gulyasyalex/Proiect-NXP-CUP-2025-/Teensy-Code/Images/20240411_223237.jpg

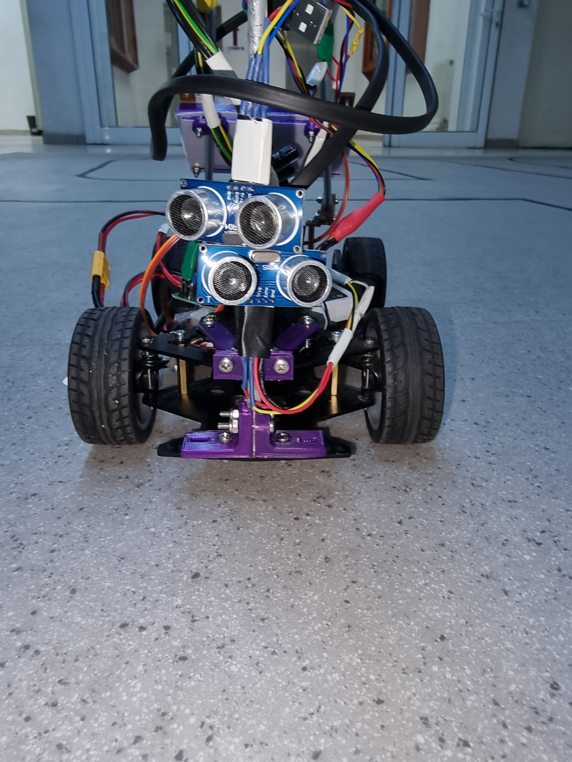
Teensy-Code/Images/20240411_223237.jpg
