gulyasyalex/Proiect-NXP-CUP-2025-/Teensy-Code/Images/20240411_223405.jpg

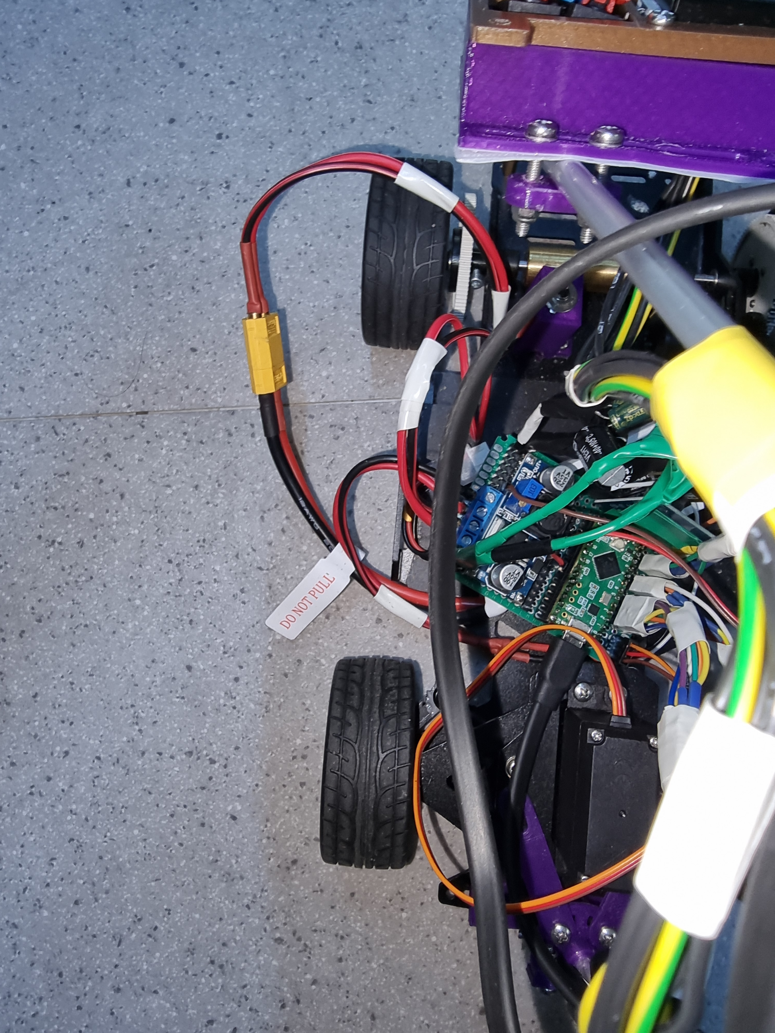
Teensy-Code/Images/20240411_223405.jpg
