gulyasyalex/Proiect-NXP-CUP-2025-/Teensy-Code/Images/20240411_223413.jpg

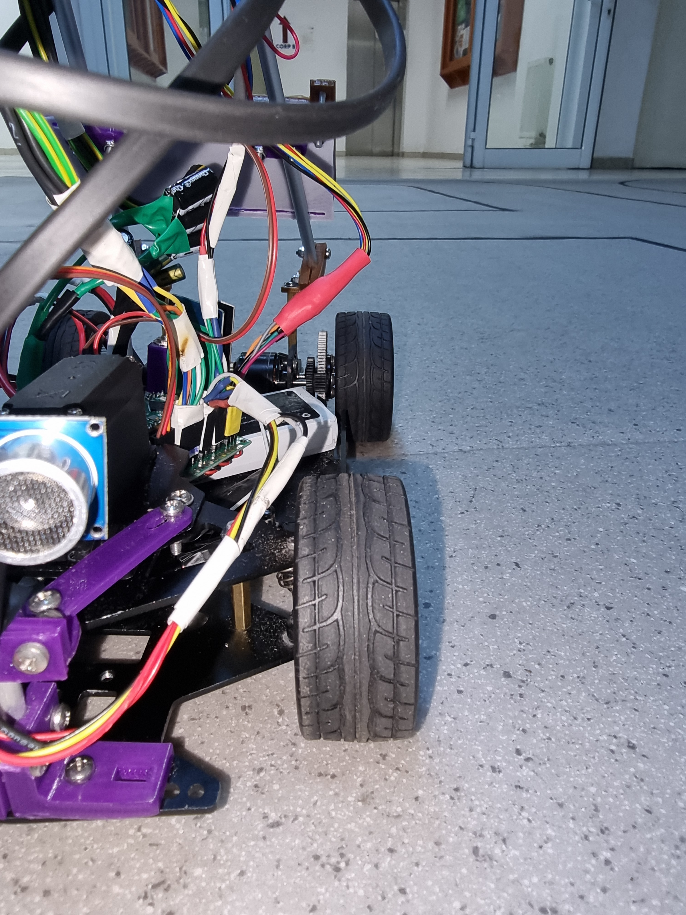
Teensy-Code/Images/20240411_223413.jpg
