gulyasyalex/Proiect-NXP-CUP-2025-/Teensy-Code/Images/20240411_223524.jpg

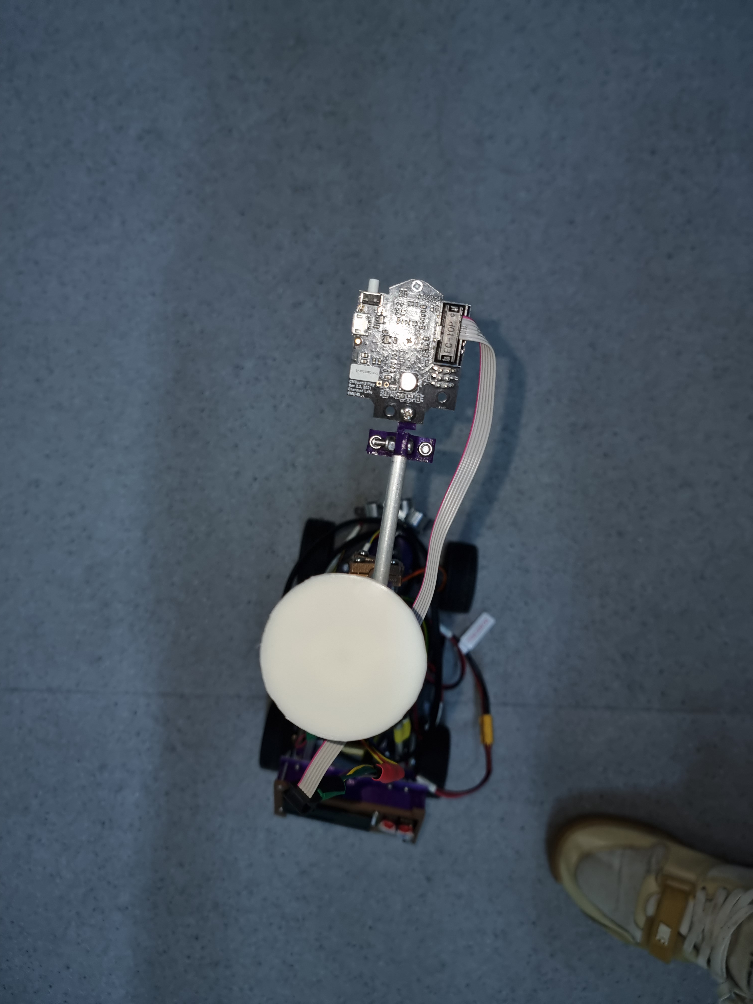
Teensy-Code/Images/20240411_223524.jpg
