gulyasyalex/Proiect-NXP-CUP-2025-/Teensy-Code/Images/car.jpg

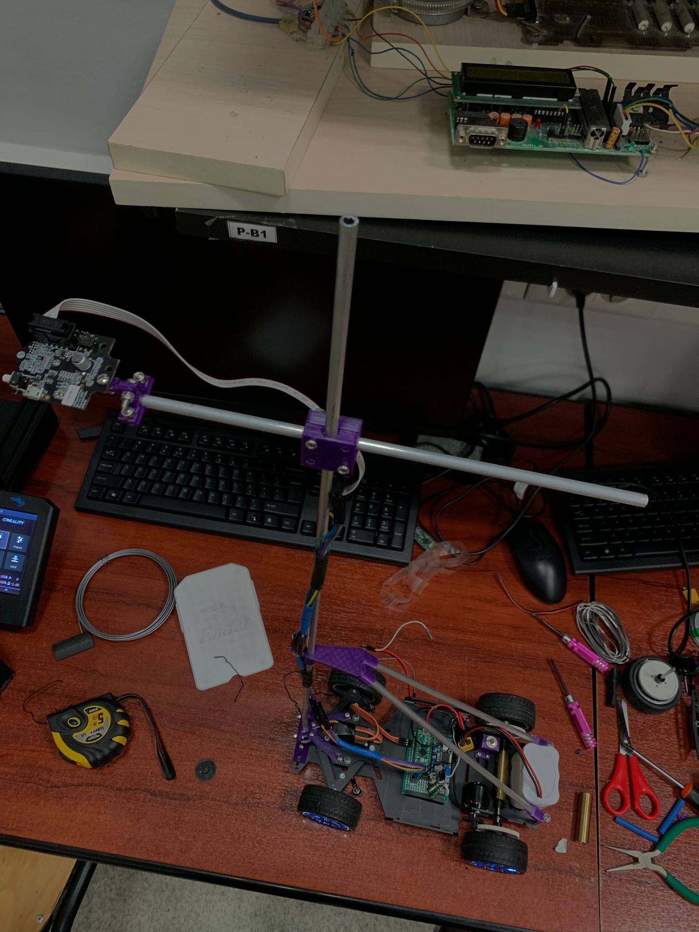
Teensy-Code/Images/car.jpg
