gulyasyalex/Proiect-NXP-CUP-2025-/Teensy-Code/Images/carMenu1.jpg

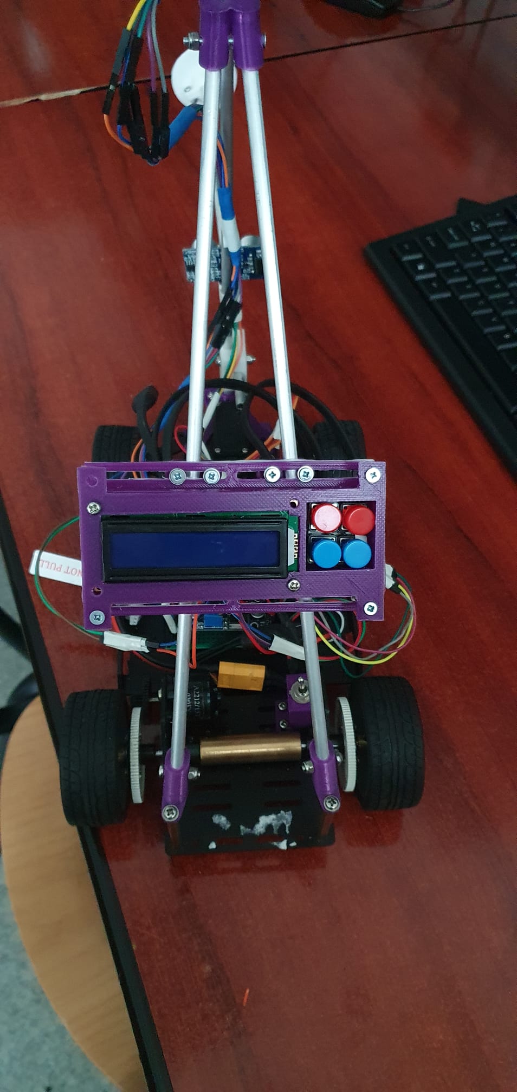
Teensy-Code/Images/carMenu1.jpg
