gulyasyalex/Proiect-NXP-CUP-2025-/Teensy-Code/Images/CarMenu.jpg

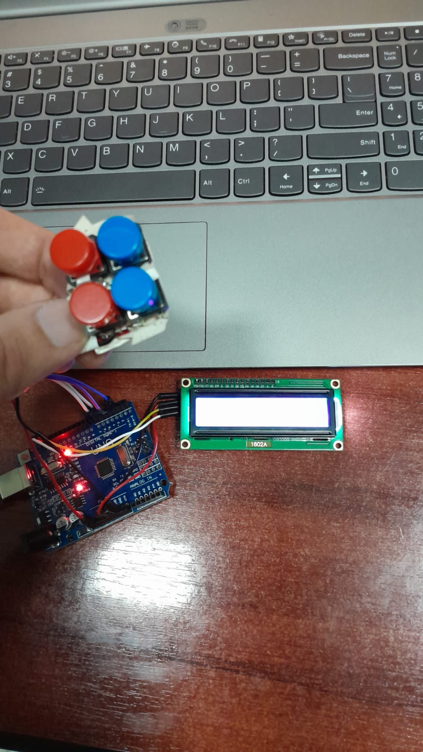
Teensy-Code/Images/CarMenu.jpg
