gulyasyalex/Proiect-NXP-CUP-2025-/Teensy-Code/Images/CarPcb.jpg

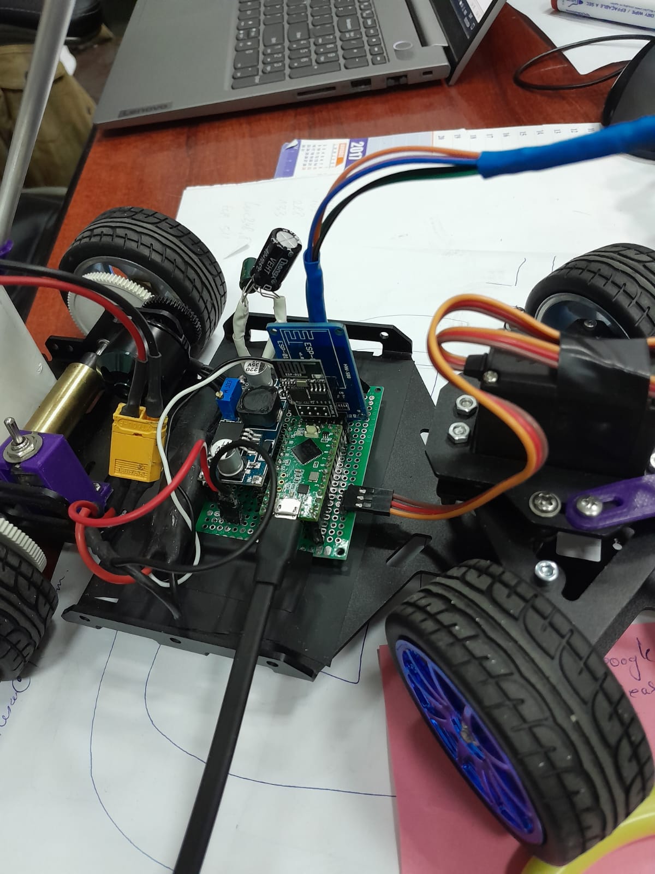
Teensy-Code/Images/CarPcb.jpg
