gulyasyalex/Proiect-NXP-CUP-2025-/Teensy-Code/Images/carVersion3.jpg

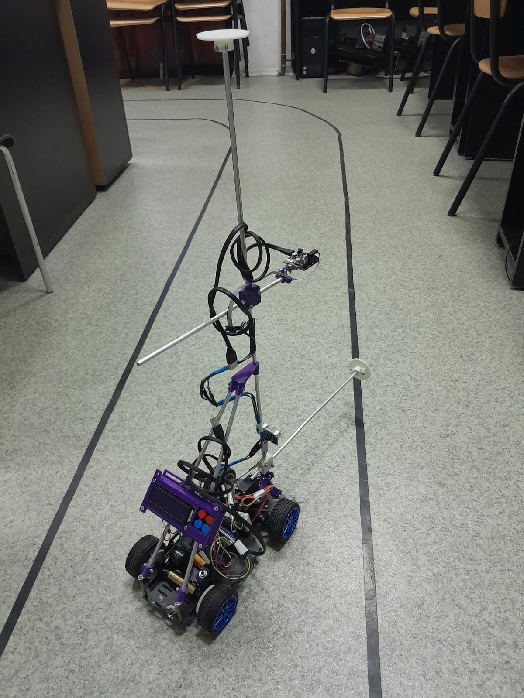
Teensy-Code/Images/carVersion3.jpg
