gulyasyalex/Proiect-NXP-CUP-2025-/Teensy-Code/Images/lcd_menu_support.png

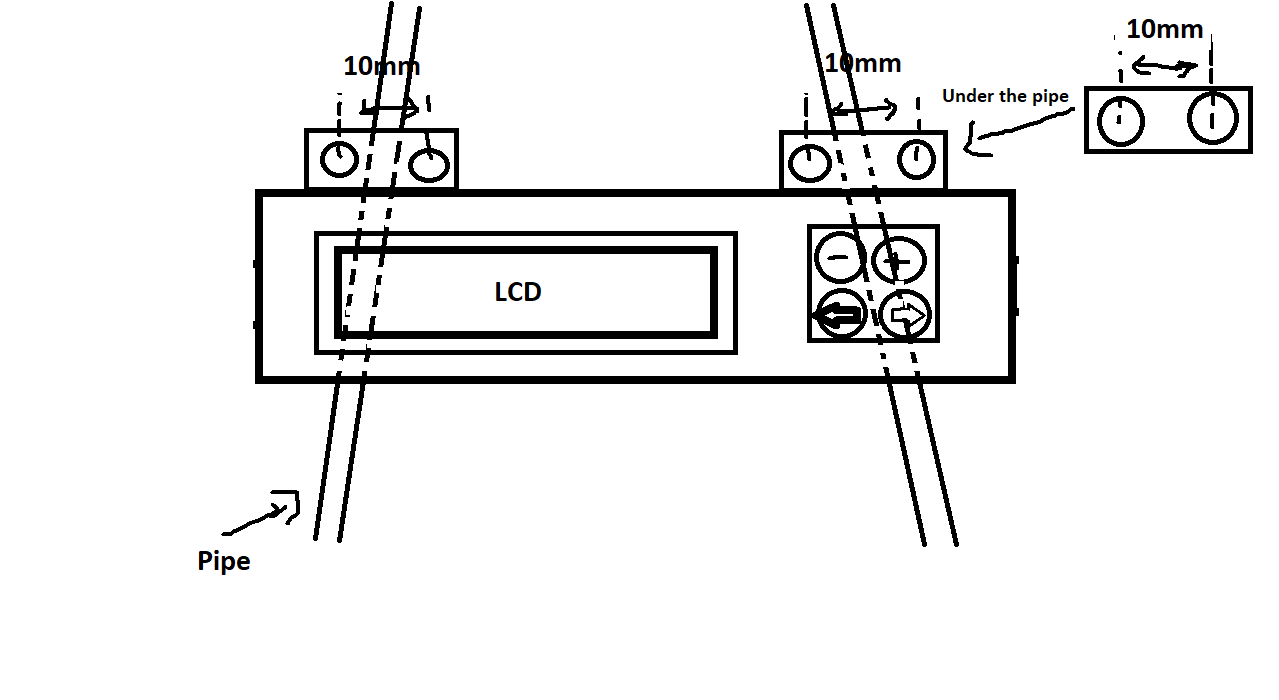
Teensy-Code/Images/lcd_menu_support.png
