gulyasyalex/Proiect-NXP-CUP-2025-/Teensy-Code/PCB-Kicad/Modul_Lcd_Butoane/lcd3dModel.jpeg

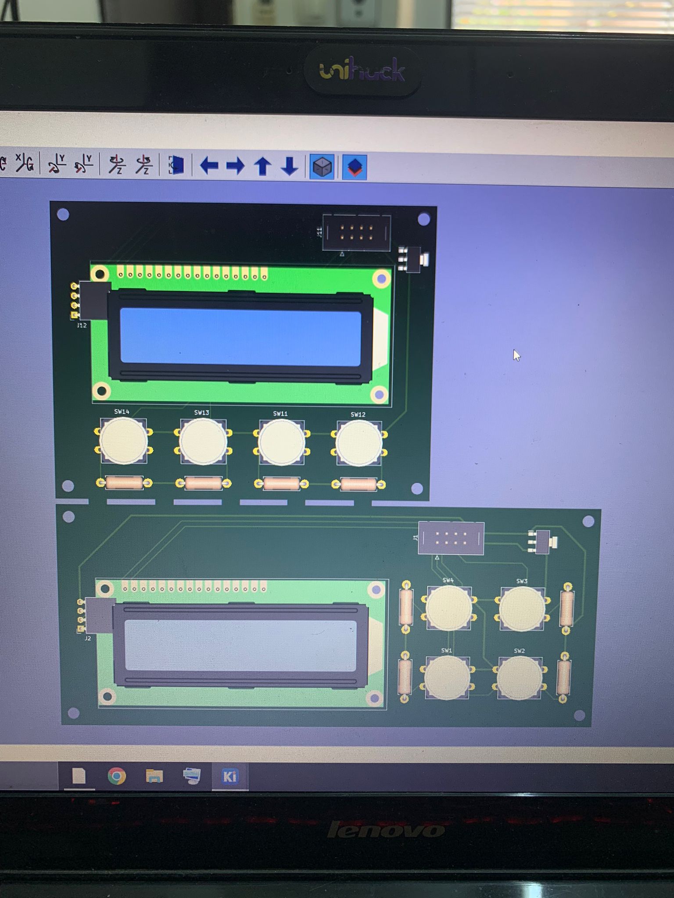
Teensy-Code/PCB-Kicad/Modul_Lcd_Butoane/lcd3dModel.jpeg
