gulyasyalex/Proiect-NXP-CUP-2025-/Teensy-Code/PCB-Kicad/Modul_Main_Board/PCB_FRONT.jpeg

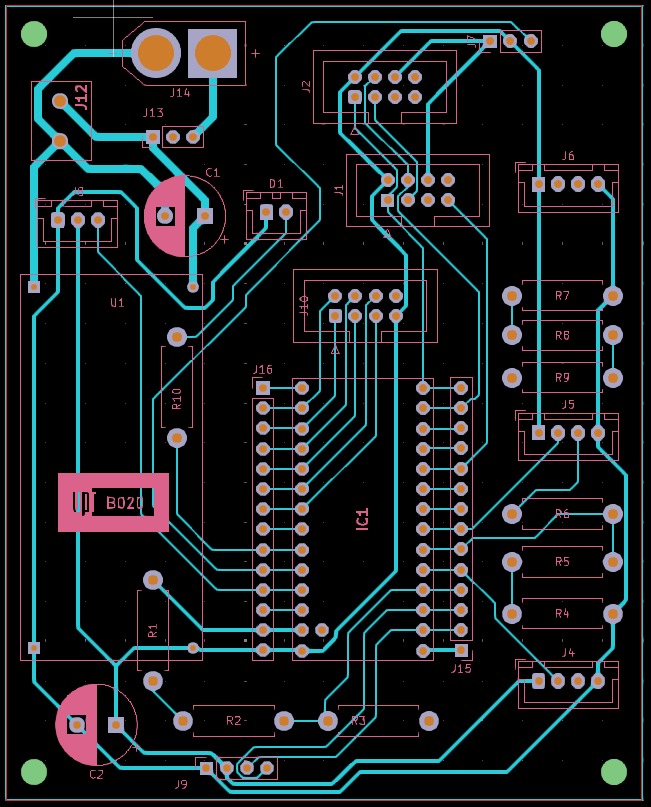
Teensy-Code/PCB-Kicad/Modul_Main_Board/PCB_FRONT.jpeg
