gulyasyalex/Proiect-NXP-CUP-2025-/VisionDebixTCP/lines2.jpeg

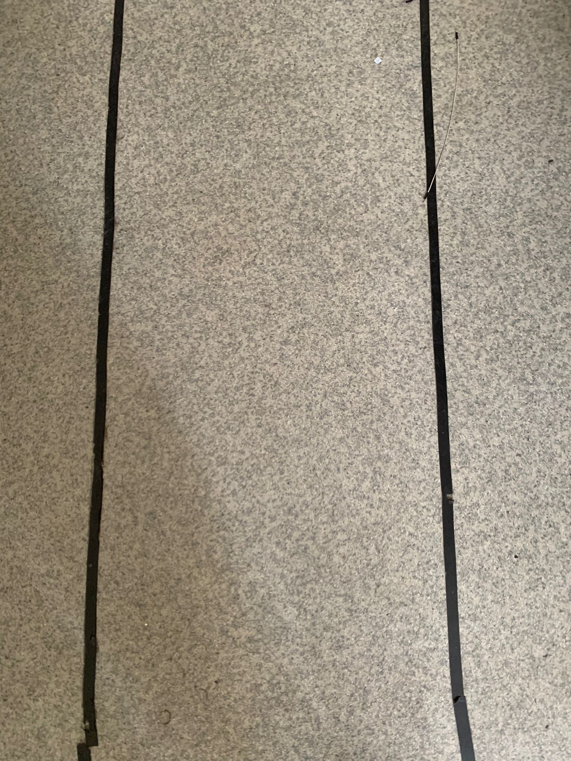
VisionDebixTCP/lines2.jpeg
