gulyasyalex/Proiect-NXP-CUP-2025-/VisionDebixTCP/lines3.jpeg

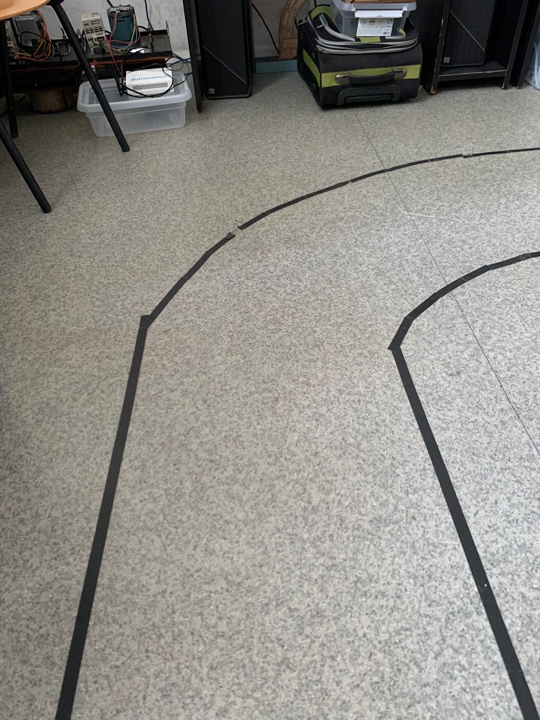
VisionDebixTCP/lines3.jpeg
