gulyasyalex/Proiect-NXP-CUP-2025-/VisionDebixTCP/lines.jpeg

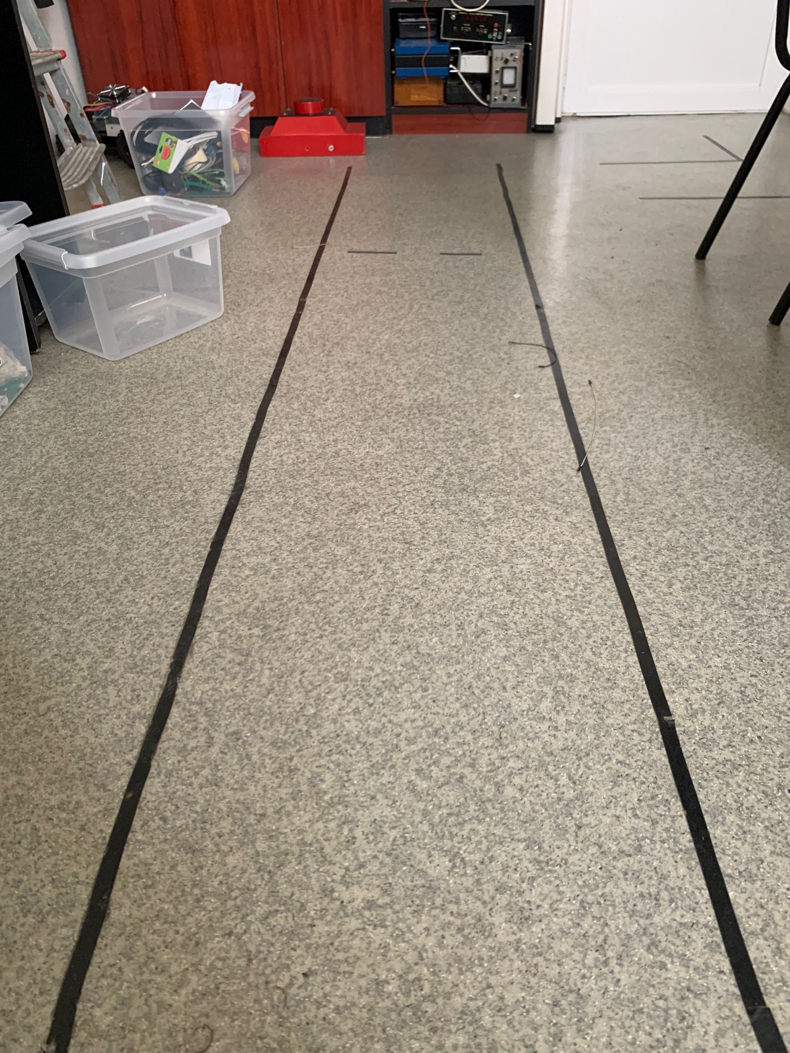
VisionDebixTCP/lines.jpeg
