gulyasyalex/Proiect-NXP-CUP-2025-/Teensy-Code/3D Print/Camera/Camera stand/round joint/round joint_arm.stl

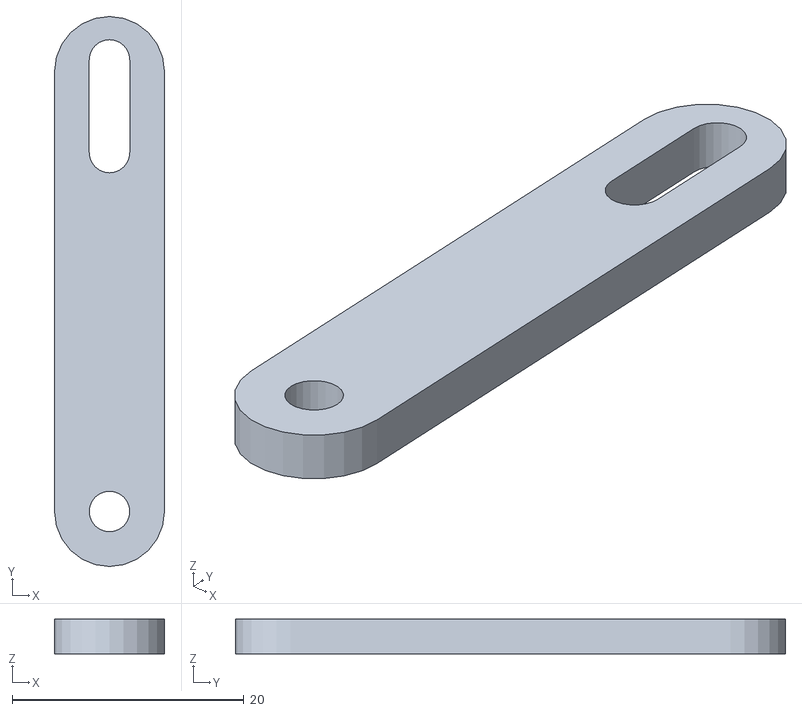
[picture p59: CAD file, 2025-06-28]
Teensy-Code/3D Print/Camera/Camera stand/round joint/round joint_arm.stl
9.50 x 47.5 x 3.00
