gulyasyalex/Proiect-NXP-CUP-2025-/Teensy-Code/3D Print/Camera/TopCameraStandSafetyProtection/TopCameraStandSafetyProtection_round_joint.stl

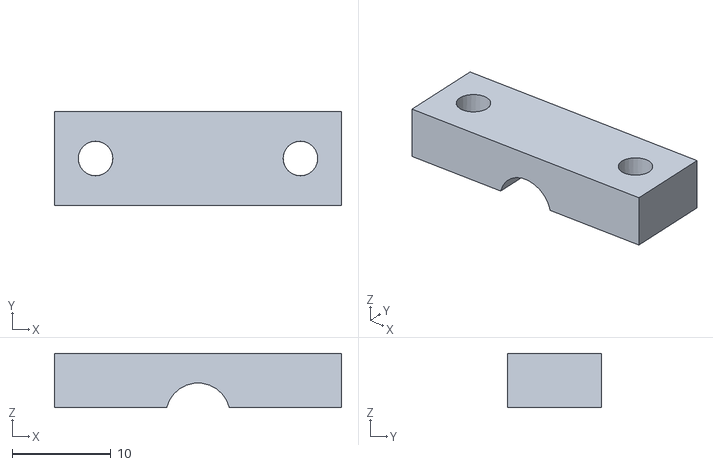
[picture p60: CAD file, 2025-06-28]
Teensy-Code/3D Print/Camera/TopCameraStandSafetyProtection/TopCameraStandSafetyProtection_round_joint.stl
29.0 x 9.50 x 5.50
