gulyasyalex/Proiect-NXP-CUP-2025-/Teensy-Code/3D Print/CarModel/RearMotorRodPilloBlock_RpmSensorSupport.3mf

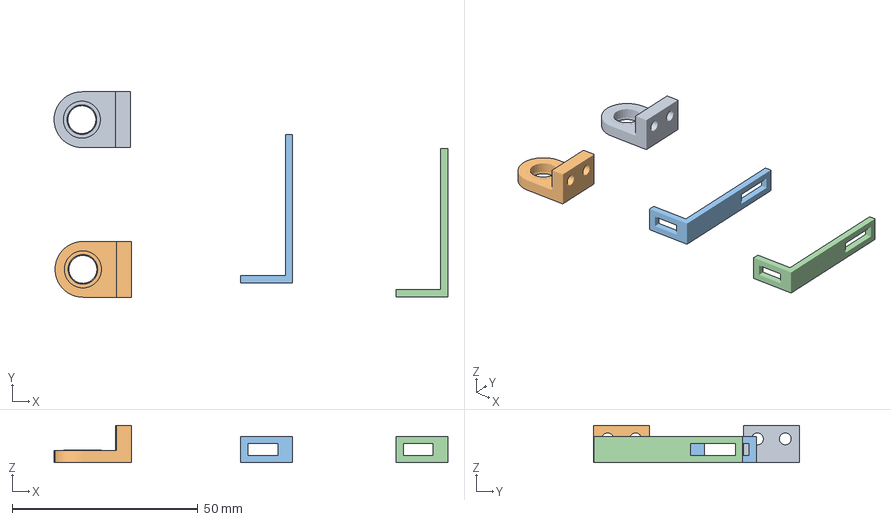
[picture p61: CAD file, 2025-06-28]
Teensy-Code/3D Print/CarModel/RearMotorRodPilloBlock_RpmSensorSupport.3mf
106.0 x 55.3 x 10.0 mm
RearMotorRodPilloBlock.stl x 2
RpmSensorSupport.stl x 2
