gulyasyalex/Proiect-NXP-CUP-2025-/Teensy-Code/3D Print/MenuButtons/Minus.stl

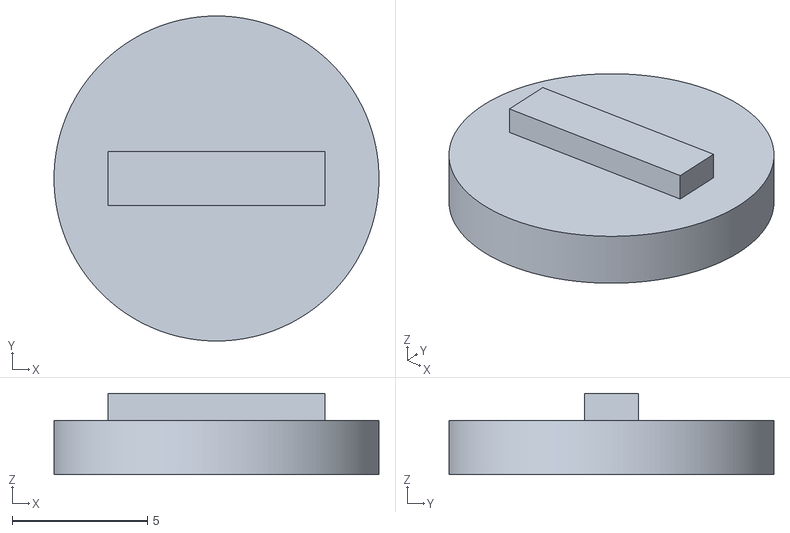
[picture p62: CAD file, 2025-06-28]
Teensy-Code/3D Print/MenuButtons/Minus.stl
12.0 x 12.0 x 3.00
