gulyasyalex/Proiect-NXP-CUP-2025-/Teensy-Code/3D Print/NXPCupTimer/CutieTimer.stl

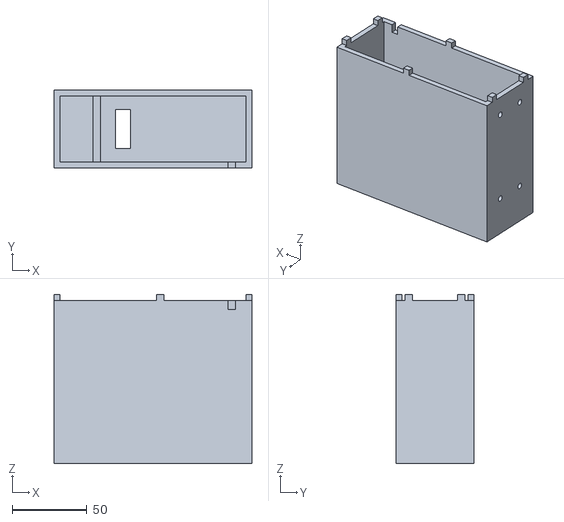
[picture p63: CAD file, 2025-06-28]
Teensy-Code/3D Print/NXPCupTimer/CutieTimer.stl
132.0 x 52.0 x 113.0
