gulyasyalex/Proiect-NXP-CUP-2025-/Teensy-Code/3D Print/Camera/Camera joint/camera joint_arm.stl

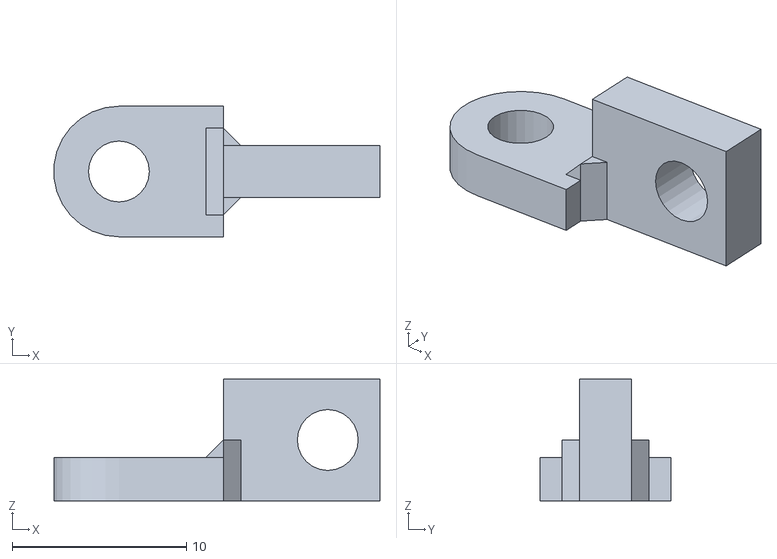
[picture p64: CAD file, 2025-06-28]
Teensy-Code/3D Print/Camera/Camera joint/camera joint_arm.stl
18.7 x 7.50 x 7.00
