gulyasyalex/Proiect-NXP-CUP-2025-/Teensy-Code/3D Print/Camera/Camera stand/round joint/CE3E3V2_round joint.3mf

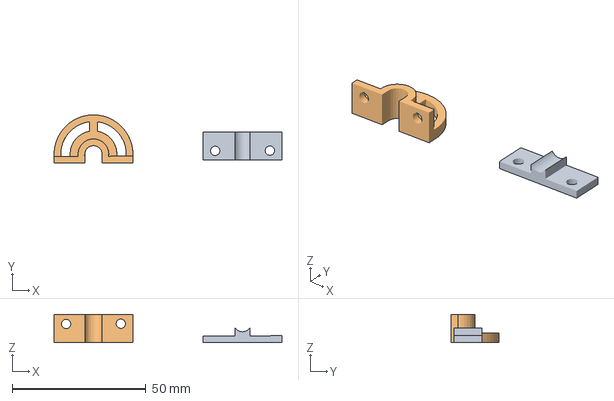
[picture p66: CAD file, 2025-06-28]
Teensy-Code/3D Print/Camera/Camera stand/round joint/CE3E3V2_round joint.3mf
85.2 x 18.1 x 10.6 mm
round joint_back.stl
round joint_front.stl
