gulyasyalex/Proiect-NXP-CUP-2025-/Teensy-Code/3D Print/CarModel/RearMotorRodPilloBlock.stl

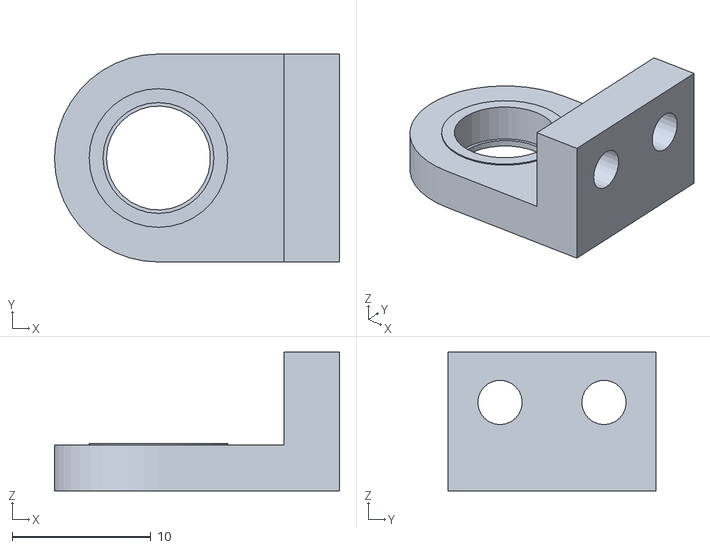
[picture p67: CAD file, 2025-06-28]
Teensy-Code/3D Print/CarModel/RearMotorRodPilloBlock.stl
20.6 x 15.0 x 10.0
