gulyasyalex/Proiect-NXP-CUP-2025-/Teensy-Code/3D Print/Camera/Camera joint/camera joint_round_1.stl

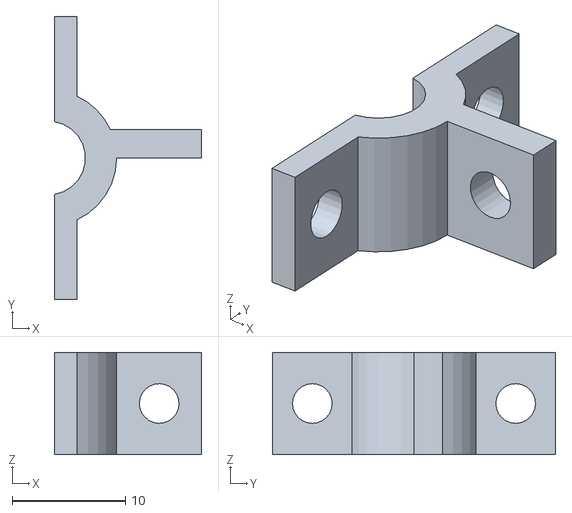
[picture p68: CAD file, 2025-06-28]
Teensy-Code/3D Print/Camera/Camera joint/camera joint_round_1.stl
13.0 x 25.0 x 9.00
