gulyasyalex/Proiect-NXP-CUP-2025-/Teensy-Code/3D Print/Camera/Camera stand longitudinal support/CE3E3V2_Camera stand longitudinal support.3mf

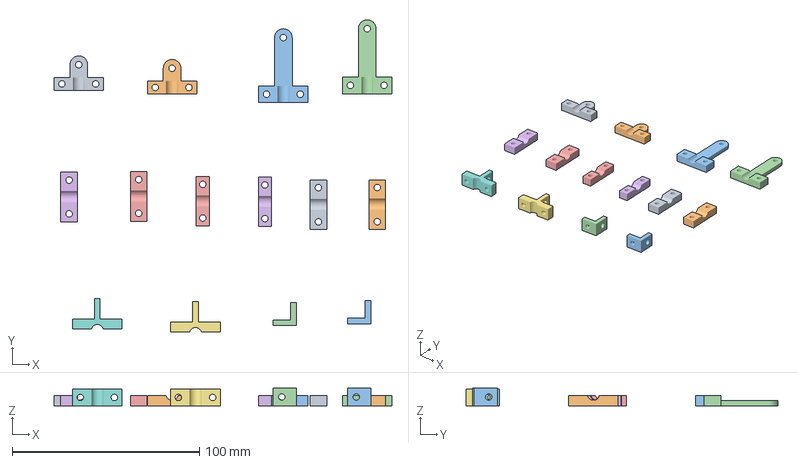
[picture p71: CAD file, 2025-06-28]
Teensy-Code/3D Print/Camera/Camera stand longitudinal support/CE3E3V2_Camera stand longitudinal support.3mf
180.5 x 166.9 x 9.50 mm
Camera stand longitudinal support_vertical pipe joint_2.stl
Camera stand longitudinal support_vertical pipe joint_2.stl(1)
Camera stand longitudinal support_longitudinal pipe joint_1.stl
Camera stand longitudinal support_longitudinal pipe joint_1.stl(1)
Camera stand longitudinal support_longitudinal pipe joint_2.stl
Camera stand longitudinal support_longitudinal pipe joint_2.stl(1)
Camera stand longitudinal support_vertical pipe joint_1.stl
Camera stand longitudinal support_vertical pipe joint_1.stl(1)
Camera stand longitudinal support_longitudinal pipe joint back_1.stl
Camera stand longitudinal support_longitudinal pipe joint back_1.stl(1)
Camera stand longitudinal support_chassis joint.stl
Camera stand longitudinal support_chassis joint.stl(1)
Camera stand longitudinal support_longitudinal pipe joint back_2.stl(2)
Camera stand longitudinal support_longitudinal pipe joint back_2.stl(1)
