gulyasyalex/Proiect-NXP-CUP-2025-/Teensy-Code/3D Print/Camera/Camera stand/round joint/round joint_front.stl

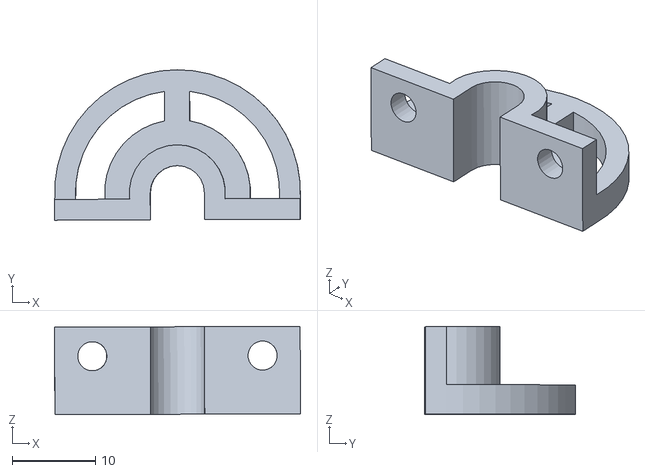
[picture p72: CAD file, 2025-06-28]
Teensy-Code/3D Print/Camera/Camera stand/round joint/round joint_front.stl
29.5 x 18.1 x 10.6
