gulyasyalex/Proiect-NXP-CUP-2025-/Teensy-Code/3D Print/CarModel/CassisPlateBackend.3mf

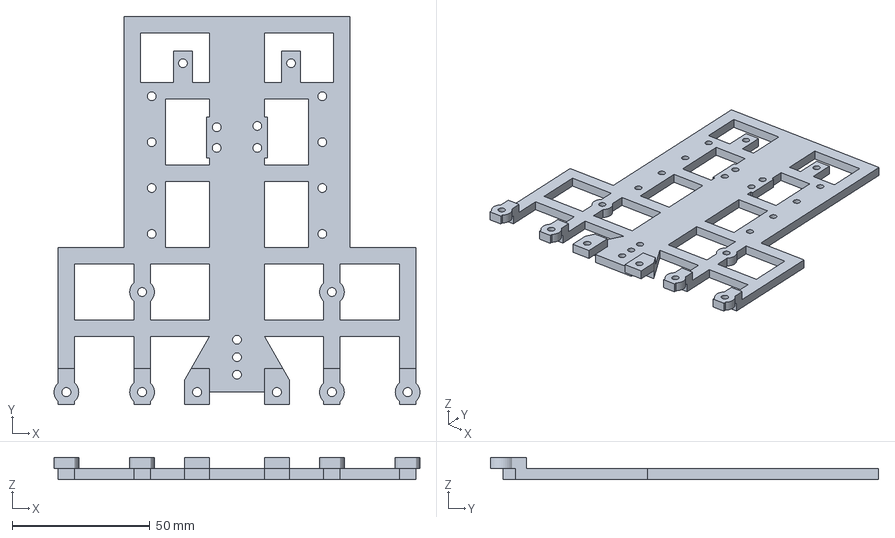
[picture p73: CAD file, 2025-06-28]
Teensy-Code/3D Print/CarModel/CassisPlateBackend.3mf
133.0 x 141.0 x 8.00 mm
