gulyasyalex/Proiect-NXP-CUP-2025-/Teensy-Code/3D Print/CarModel/RpmSensorSupport.stl

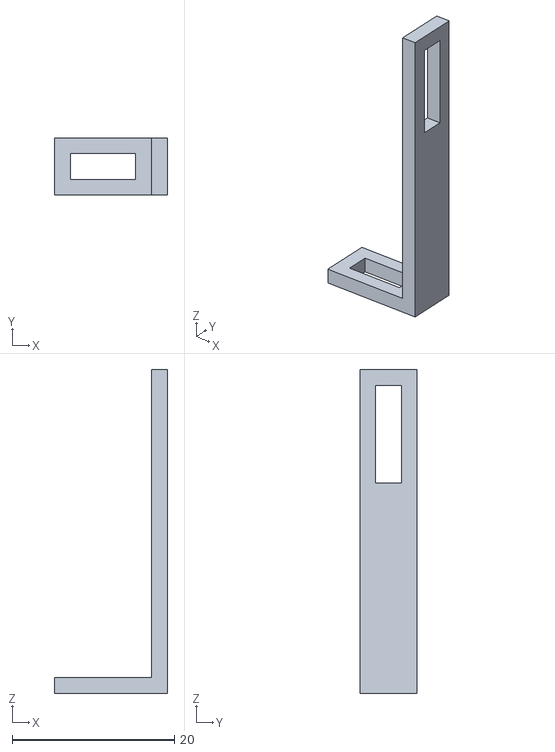
[picture p74: CAD file, 2025-06-28]
Teensy-Code/3D Print/CarModel/RpmSensorSupport.stl
14.0 x 7.00 x 40.0
