gulyasyalex/Proiect-NXP-CUP-2025-/Teensy-Code/3D Print/CarModel/CarBodyFrontEnd.stl

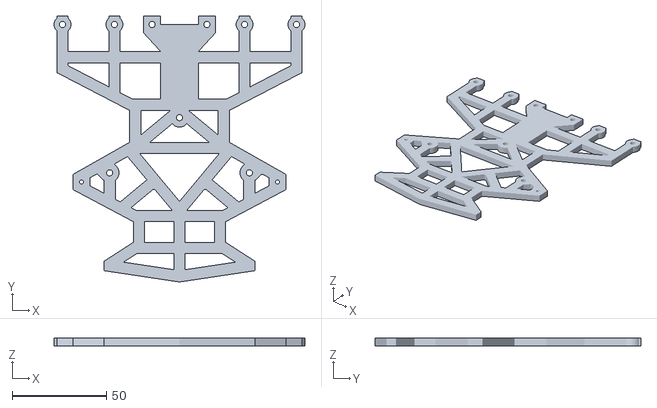
[picture p75: CAD file, 2025-06-28]
Teensy-Code/3D Print/CarModel/CarBodyFrontEnd.stl
133.0 x 141.0 x 4.00
