gulyasyalex/Proiect-NXP-CUP-2025-/Teensy-Code/3D Print/Camera/Camera stand longitudinal support/Camera stand longitudinal support_vertical pipe joint_1.stl

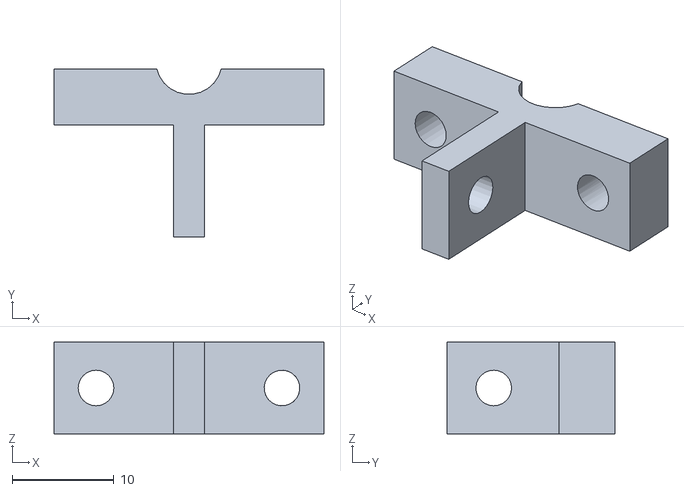
[picture p76: CAD file, 2025-06-28]
Teensy-Code/3D Print/Camera/Camera stand longitudinal support/Camera stand longitudinal support_vertical pipe joint_1.stl
26.5 x 16.5 x 9.00
