gulyasyalex/Proiect-NXP-CUP-2025-/Teensy-Code/3D Print/Camera/Camera stand longitudinal support/Camera stand longitudinal support_longitudinal pipe joint back_1.stl

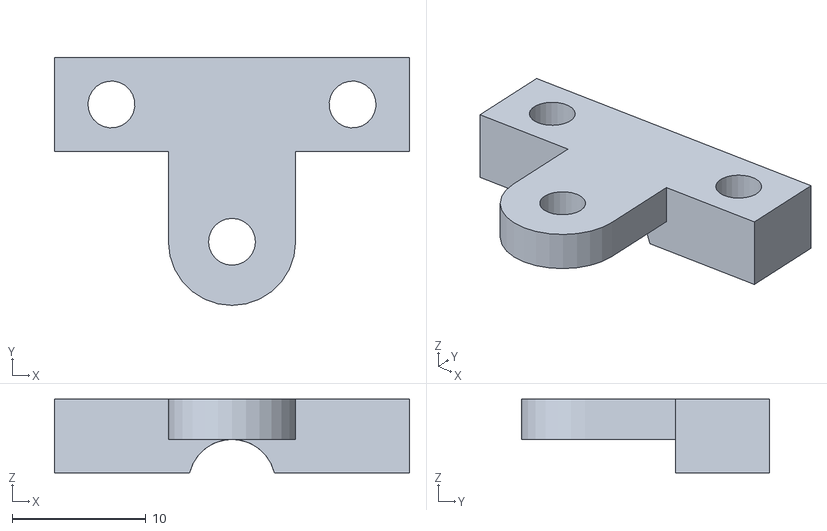
[picture p77: CAD file, 2025-06-28]
Teensy-Code/3D Print/Camera/Camera stand longitudinal support/Camera stand longitudinal support_longitudinal pipe joint back_1.stl
26.5 x 18.5 x 5.50
