gulyasyalex/Proiect-NXP-CUP-2025-/Teensy-Code/3D Print/Camera/Camera joint/image.PNG

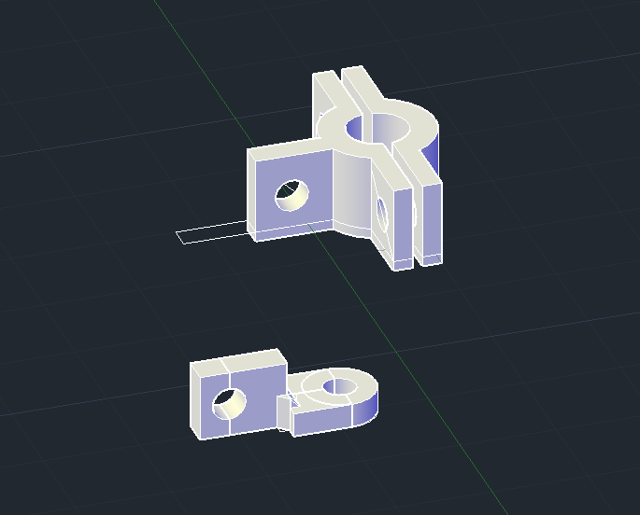
Teensy-Code/3D Print/Camera/Camera joint/image.PNG
