gulyasyalex/Proiect-NXP-CUP-2025-/Teensy-Code/3D Print/Camera/Camera stand/90 degrees short L/image.PNG

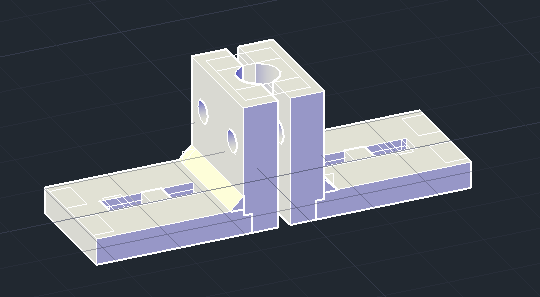
Teensy-Code/3D Print/Camera/Camera stand/90 degrees short L/image.PNG
