gulyasyalex/Proiect-NXP-CUP-2025-/Teensy-Code/3D Print/CarBodyAdditionalMounting/MountingPlatePCBs/MountingPlatePCBs.PNG

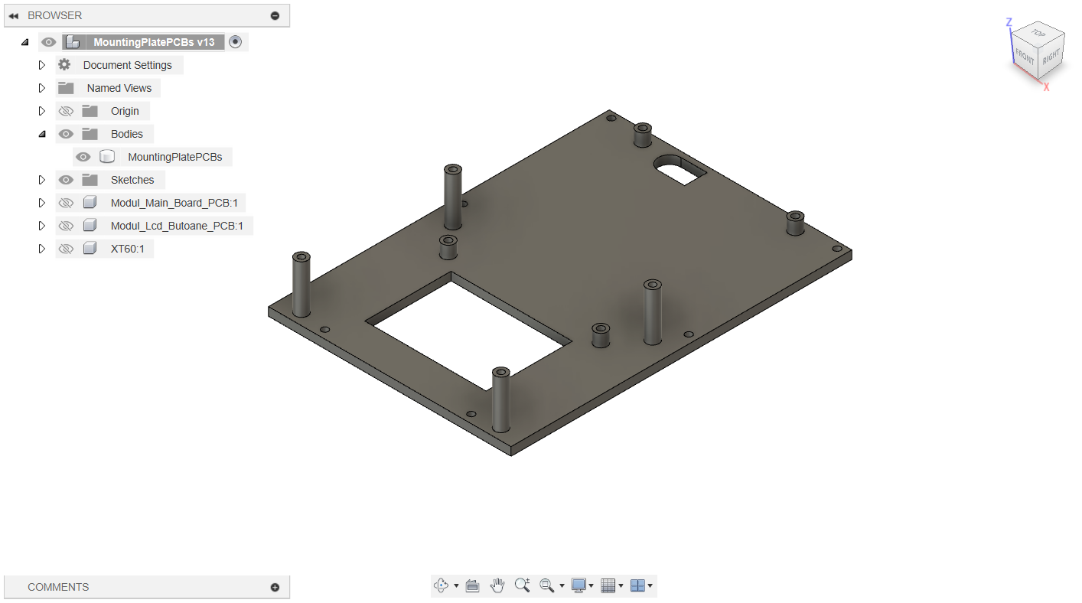
Teensy-Code/3D Print/CarBodyAdditionalMounting/MountingPlatePCBs/MountingPlatePCBs.PNG
