gulyasyalex/Proiect-NXP-CUP-2025-/Teensy-Code/3D Print/MenuButtons/Left.PNG

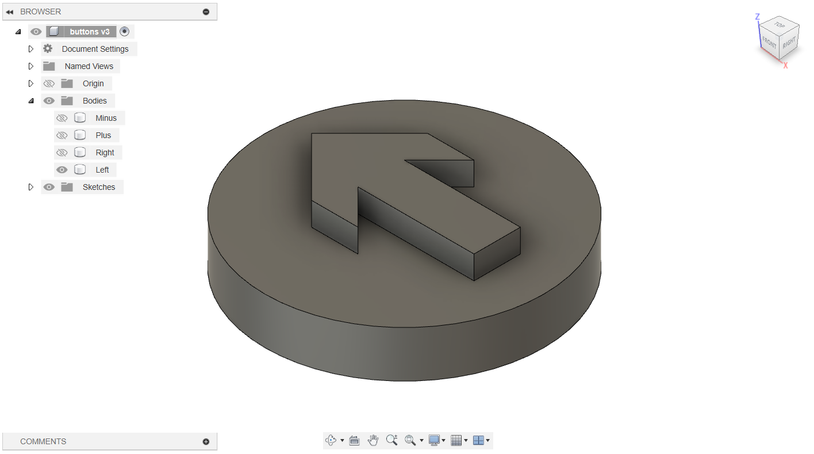
Teensy-Code/3D Print/MenuButtons/Left.PNG
