gulyasyalex/Proiect-NXP-CUP-2025-/Teensy-Code/3D Print/WheelArm12by4mm/WheelArm12by4mm.PNG

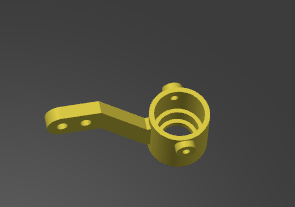
Teensy-Code/3D Print/WheelArm12by4mm/WheelArm12by4mm.PNG
