gulyasyalex/Proiect-NXP-CUP-2025-/Teensy-Code/Wiring_bb.jpg

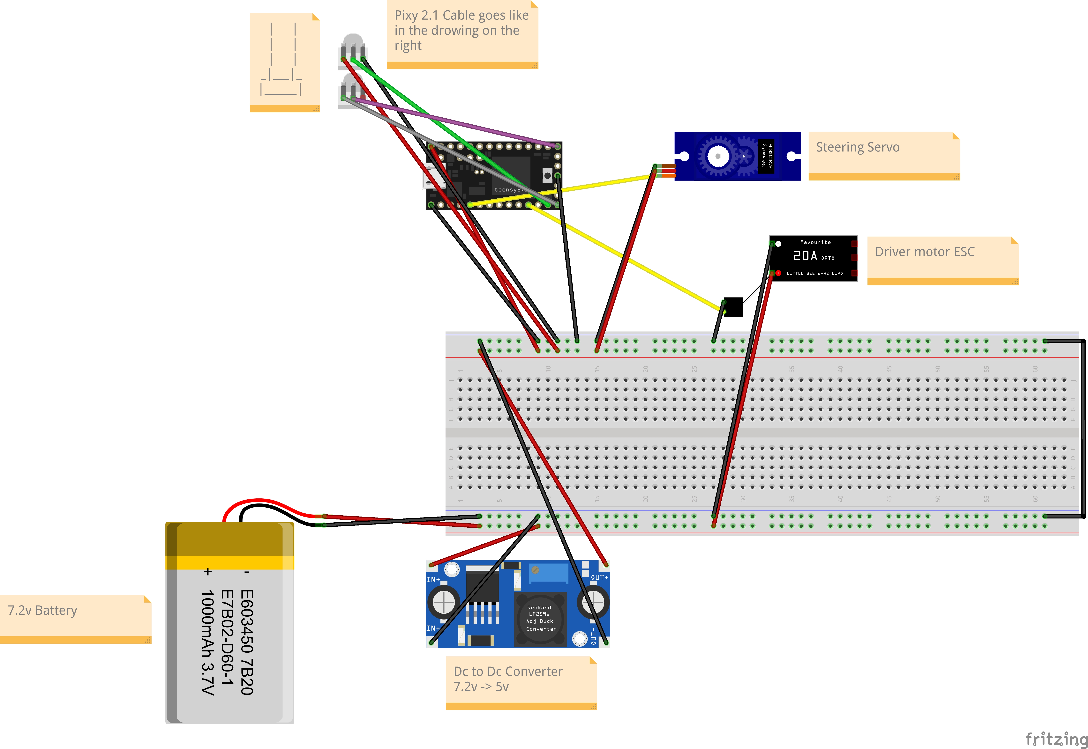
Teensy-Code/Wiring_bb.jpg
