gulyasyalex/Proiect-NXP-CUP-2025-/testImages/imagine03032025_01.jpg

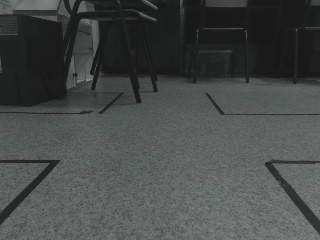
testImages/imagine03032025_01.jpg
