gulyasyalex/Proiect-NXP-CUP-2025-/testImages/imagine08122024_01.jpg

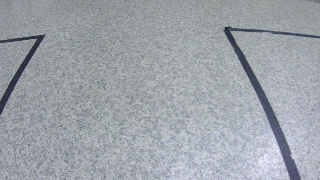
testImages/imagine08122024_01.jpg
