gulyasyalex/Proiect-NXP-CUP-2025-/testImages/imagine08122024_02.jpg

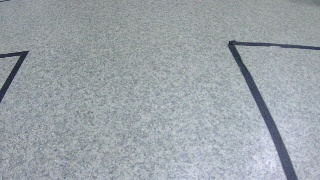
testImages/imagine08122024_02.jpg
