gulyasyalex/Proiect-NXP-CUP-2025-/testImages/imagine08122024_05.jpg

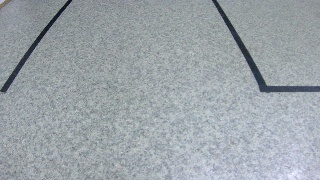
testImages/imagine08122024_05.jpg
