gulyasyalex/Proiect-NXP-CUP-2025-/testImages/imagine08122024_08.jpg

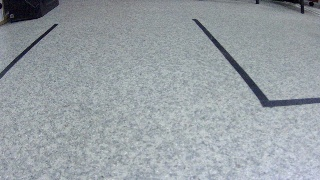
testImages/imagine08122024_08.jpg
