gulyasyalex/Proiect-NXP-CUP-2025-/testImages/imagine09122024_01.jpg

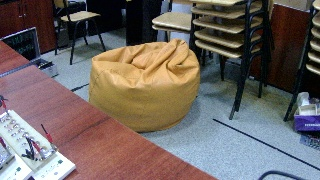
testImages/imagine09122024_01.jpg
