gulyasyalex/Proiect-NXP-CUP-2025-/testImages/imagine12022024_02.jpg

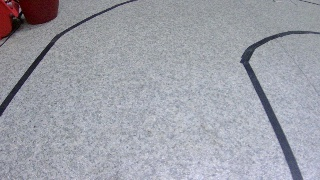
testImages/imagine12022024_02.jpg
