gulyasyalex/Proiect-NXP-CUP-2025-/testImages/imagineSala2.jpg

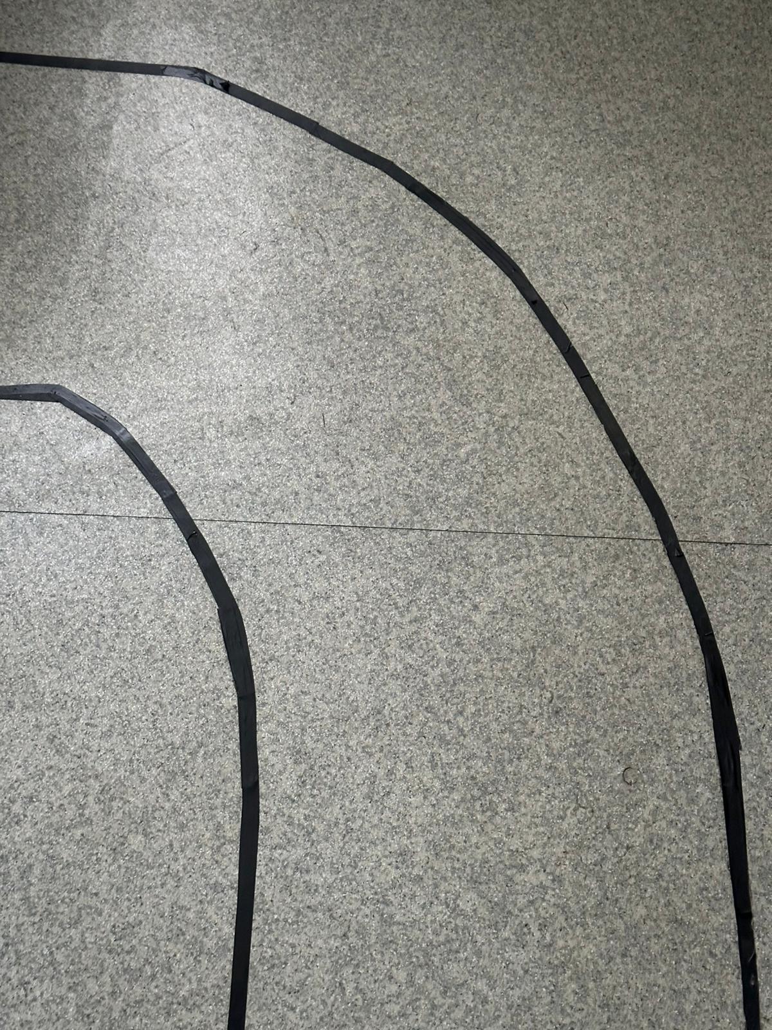
testImages/imagineSala2.jpg
