gulyasyalex/Proiect-NXP-CUP-2025-/testImages/imagineSala3.jpg

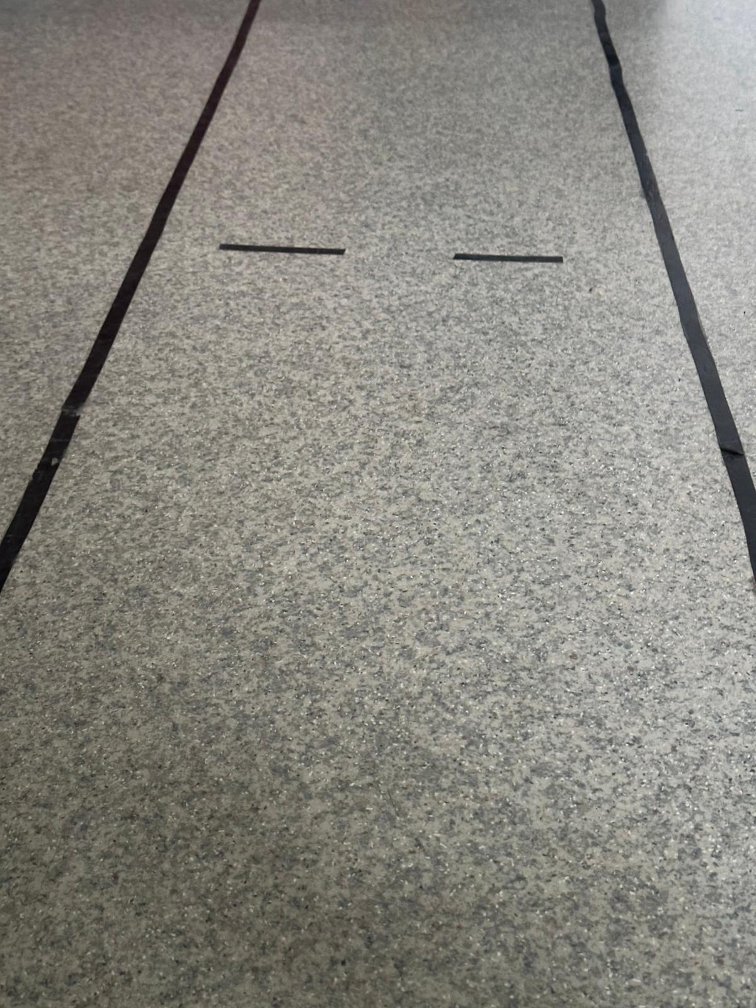
testImages/imagineSala3.jpg
