gulyasyalex/Proiect-NXP-CUP-2025-/testImages/imagineSala4.jpg

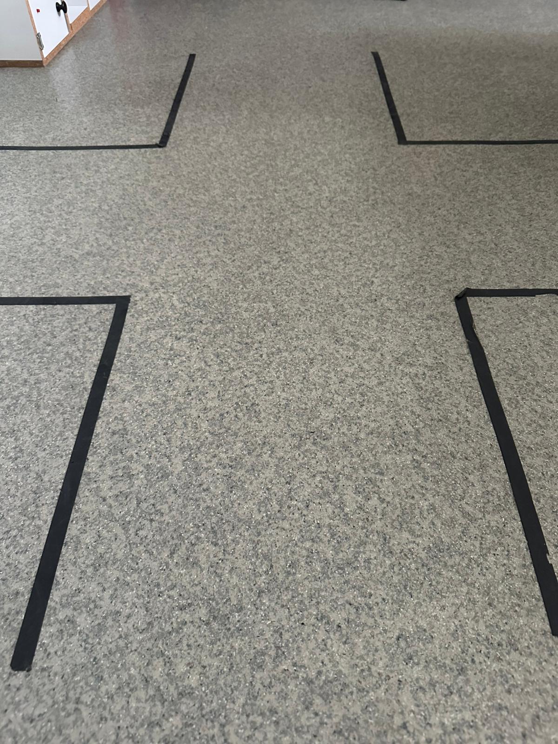
testImages/imagineSala4.jpg
