gulyasyalex/Proiect-NXP-CUP-2025-/testImages/imagineThreshold_01.jpg

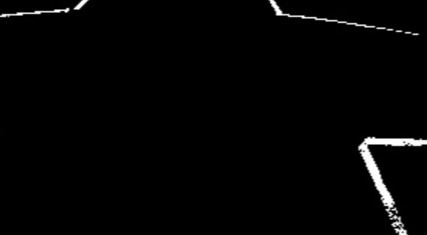
testImages/imagineThreshold_01.jpg
