gulyasyalex/Proiect-NXP-CUP-2025-/testImages/imagineThreshold_02.jpg

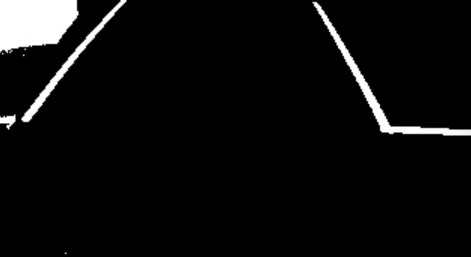
testImages/imagineThreshold_02.jpg
