gulyasyalex/Proiect-NXP-CUP-2025-/testImages/imagineThreshold_03.jpg

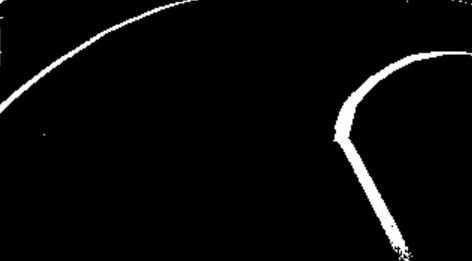
testImages/imagineThreshold_03.jpg
