gulyasyalex/Proiect-NXP-CUP-2025-/testImages/imagineThreshold_04.jpg

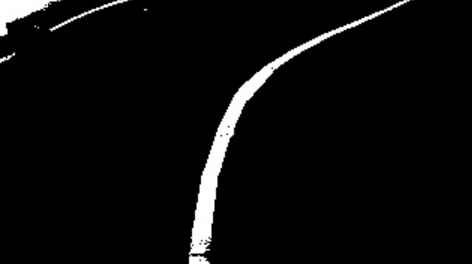
testImages/imagineThreshold_04.jpg
