gulyasyalex/Proiect-NXP-CUP-2025-/testImages/lines4.jpeg

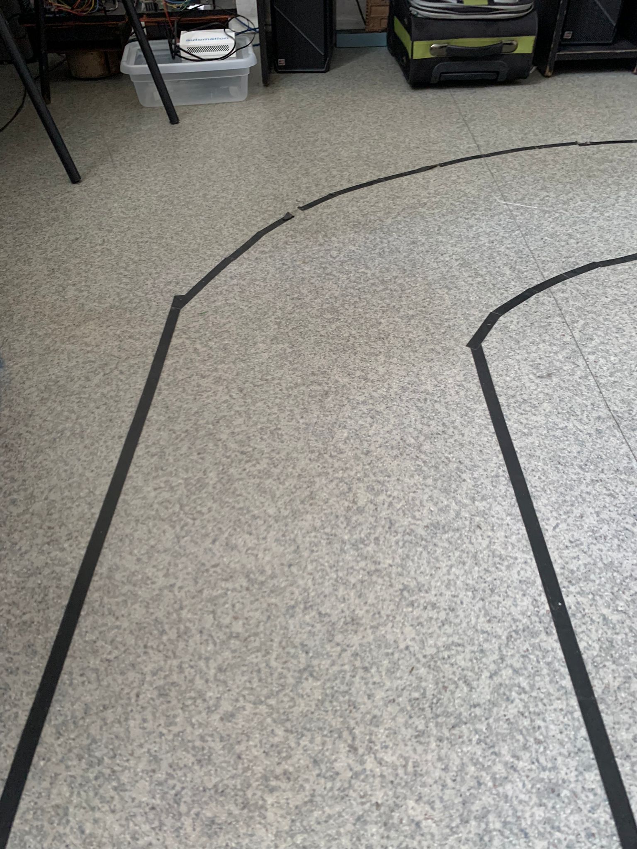
testImages/lines4.jpeg
