gulyasyalex/Proiect-NXP-CUP-2025-/testImages/lines5.jpeg

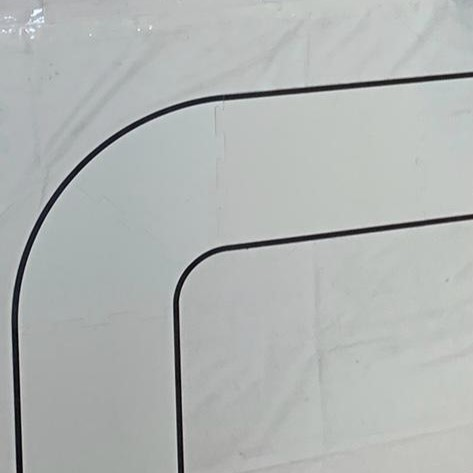
testImages/lines5.jpeg
