gulyasyalex/Proiect-NXP-CUP-2025-/testImages/ogImage.jpg

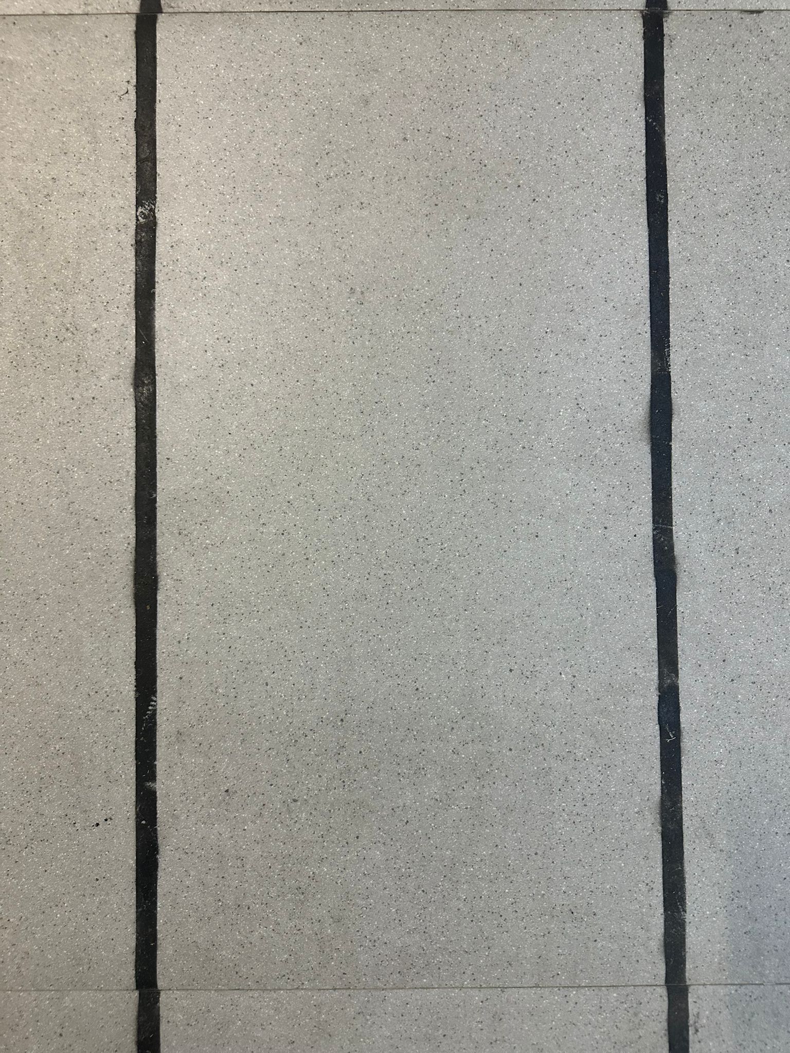
testImages/ogImage.jpg
