gulyasyalex/Proiect-NXP-CUP-2025-/src/main.cpp

#include <iostream>
#include <thread>
#include <vector>
#include <memory>
#include <csignal>
#include <chrono>
#include <cstring>

// Needed for Shared Memory access
#include <fcntl.h>                                  // Needed for O_CREAT, O_RDWR flags in shm_open()
#include <sys/mman.h>                               // Required for mmap(), shm_open(), and munmap()
#include <unistd.h>                                 // Required for ftruncate(), sleep(), and close()

#include "SerialPortFunctions/SerialPort.hpp"
#include "CameraFunctions/CameraProcessing.hpp"
#include "CameraFunctions/cameraSetup.h"
#include "config.h"

#include <sys/wait.h>
#include <gpiod.h>

#include <cstddef>  // Required for `offsetof`
#include "json.hpp"
#include "SharedConfigJson.hpp"


std::atomic<pid_t> child_pid(-1);  
std::atomic<bool> app_running{true};

// Global shared pointer for managing the camera
std::shared_ptr<CameraProcessing> global_camera;
std::shared_ptr<SharedConfig> global_config;
debix::SerialPort& serial = debix::SerialPort::getInstance();

#if 1 == ENABLE_TCP_SITE_DEBUG 
    TcpConnection websiteTCP{8888};
#endif

std::mutex configMutex; 

void signalHandler(int signal);
void checkButtonPress();
void websiteTCPLoop(TcpConnection& connection);
bool isValidConfig(const SharedConfig& config);

int main() {
    std::signal(SIGINT, signalHandler); // Register SIGINT handler
    std::signal(SIGSEGV, signalHandler); // Register SIGSEGV handler
    std::signal(SIGTERM, signalHandler); // Register SIGTERM handler

    #if 1 == ENABLE_TEENSY_SERIAL
        if(!serial.connectTeensy(SERIAL_PORT))
        {
            exit(1);
        }
    #endif    
    // for (int i = 0; i < 3; ++i) {
    //     serial.writeToSerial("Hello from Debix, message " + std::to_string(i));
    //     std::this_thread::sleep_for(std::chrono::seconds(1));
    // }

    // Shared memory for LCD and Rotary python code
    int shm_fd = shm_open(SHM_NAME, O_CREAT | O_RDWR, 0666);
    if ( -1 == shm_fd ){
        std::cerr << "Function shm_open failed!" << std::endl;
        return 1;
    }


    if (ftruncate(shm_fd, SHM_SIZE) == -1) {
        std::cerr << "ftruncate failed!" << std::endl;
        close(shm_fd);
        return 1;
    }

    void* mapped_mem = mmap(NULL, SHM_SIZE, PROT_READ | PROT_WRITE, MAP_SHARED, shm_fd, 0);
    if (mapped_mem == MAP_FAILED) {
        std::cerr << "Function mmap failed!" << std::endl;
        close(shm_fd);
        return 1;
    }

    global_config = std::shared_ptr<SharedConfig>(static_cast<SharedConfig*>(mapped_mem), [](SharedConfig* ptr) {
        munmap(ptr, SHM_SIZE);  // Free shared memory when `shared_ptr` is destroyed
    });

    memset(global_config.get(), 0, SHM_SIZE);

    // Initialize values
    global_config->startRace = DEFAULT_START_RACE;
    global_config->enableCarEngine = DEFAULT_ENABLE_CAR_ENGINE;
    global_config->enableCarSteering = DEFAULT_ENABLE_CAR_STEERING;
    global_config->enableCameraThresholdCheck = ENABLE_CAMERA_THRESHOLD_CHECK;
    global_config->enableFinishLineDetection = ENABLE_FINISH_LINE_DETECTION;
    global_config->currentState = FOLLOWING_LINE;
    global_config->thresholdValue = DEFAULT_THRESHOLD_VALUE;
    global_config->distanceErrorFromChassis = DEFAULT_DISTANCE_ERROR_FROM_CHASSIS;
    global_config->lineMinPixelCount = _minLinePixelCount;
    global_config->distanceSensorError = DEFAULT_DISTANCE_FROM_SENSOR_ERROR;
    global_config->stoppingDistanceBoxFrontEnd = DEFAULT_STOPPING_DISTANCE_BOX_FRONT_END;
    global_config->interpolatedPointsSetup = DEFAULT_INTERPOLATED_POINTS_SETUP;

    global_config->calibrateTopLinePerc = DEFAULT_CALIBRATE_TOP_LINE;
    global_config->calibrateBottomLinePerc = DEFAULT_CALIBRATE_BOTTOM_LINE;
    global_config->trackLaneWidthOffset = DEFAULT_TRACK_LANE_WIDTH_OFFSET;
    global_config->topImageCutPercentage = DEFAULT_TOP_IMAGE_CUT_PERCENTAGE;
    global_config->topCutOffPercentageCustomConnected = DEFAULT_TOP_CUTOFF_PERCENTAGE_CUSTOM_CONNECTED;
    global_config->lineStartPointY = DEFAULT_LINE_START_POINT_Y;
    global_config->line90DegreeAngleRange = DEFAULT_LINE_90_DEGREE_ANGLE_RANGE;
    global_config->finishLineAngleRange = DEFAULT_FINISH_LINE_ANGLE_RANGE;
    global_config->servoTurnAdjustmentCoefficient = DEFAULT_SERVO_TURN_ADJUSTMENT_COEFFICIENT;
    global_config->corneringSpeedCoefficient = DEFAULT_CORNERING_SPEED_COEFFICIENT;
    global_config->minSpeed = DEFAULT_MIN_SPEED;
    global_config->maxSpeed = DEFAULT_MAX_SPEED;
    global_config->minSpeedAfterFinish = DEFAULT_MIN_SPEED_AFTER_FINISH;
    global_config->maxSpeedAfterFinish = DEFAULT_MAX_SPEED_AFTER_FINISH;
    global_config->currentEdfFanSpeed = 0; //this is set in startRace section -> DEFAULT_EDF_FAN_CURRENT_SPEED;
    global_config->curvatureFactor = DEFAULT_CURVATURE_FACTOR;
    global_config->rdp_epsilon = DEFAULT_RDP_EPSILON;
    global_config->boostSpeedValue = DEFAULT_BOOST_SPEED_VALUE;
    global_config->minAngleLookAheadReference = DEFAULT_MIN_ANGLE_LOOKAHEAD_REFERENCE;
    global_config->maxAngleLookAheadReference = DEFAULT_MAX_ANGLE_LOOKAHEAD_REFERENCE;
    global_config->minLookAheadInCm = DEFAULT_MIN_LOOKAHEAD_IN_CM;
    global_config->maxLookAheadInCm = DEFAULT_MAX_LOOKAHEAD_IN_CM;
    global_config->waitBeforeStartSeconds = DEFAULT_WAIT_BEFORE_START_SECONDS;                      
    global_config->waitBeforeEdfStartSeconds = DEFAULT_WAIT_BEFORE_EDF_START_SECONDS;                   
    global_config->waitBeforeFinishDetectionSeconds = DEFAULT_WAIT_BEFORE_FINISH_DETECTION_SECONDS;                   

    std::cout << "Shared memory initialized with defaults: " << std::endl;

    SharedConfig* raw_config = global_config.get();  // Get raw pointer from shared_ptr

    std::cout << "\nIntegers: ";
    std::cout << raw_config->startRace << " "
            << raw_config->enableCarEngine << " "
            << raw_config->enableCarSteering << " "
            << raw_config->enableCameraThresholdCheck << " "
            << raw_config->enableFinishLineDetection << " "
            << raw_config->currentState << " "
            << raw_config->thresholdValue << " "
            << raw_config->distanceErrorFromChassis << " "
            << raw_config->lineMinPixelCount << " "
            << raw_config->distanceSensorError << " "
            << raw_config->stoppingDistanceBoxFrontEnd << " "
            << raw_config->interpolatedPointsSetup << std::endl;

    std::cout << "Doubles: ";
    std::cout << raw_config->calibrateTopLinePerc << " "
            << raw_config->calibrateBottomLinePerc << " " << " "
            << raw_config->trackLaneWidthOffset << " "
            << raw_config->topImageCutPercentage << " "
            << raw_config->topCutOffPercentageCustomConnected << " "
            << raw_config->lineStartPointY << " "
            << raw_config->line90DegreeAngleRange << " "
            << raw_config->finishLineAngleRange << " "
            << raw_config->servoTurnAdjustmentCoefficient << " "
            << raw_config->corneringSpeedCoefficient << " "
            << raw_config->minSpeed << " "
            << raw_config->maxSpeed << " "
            << raw_config->currentEdfFanSpeed << " "
            << raw_config->curvatureFactor << " "
            << raw_config->rdp_epsilon << " "
            << raw_config->boostSpeedValue << " "
            << raw_config->minAngleLookAheadReference << " "
            << raw_config->maxAngleLookAheadReference << " "
            << raw_config->minLookAheadInCm << " "
            << raw_config->maxLookAheadInCm << " "
            << raw_config->waitBeforeStartSeconds << " "
            << raw_config->waitBeforeEdfStartSeconds << " "
            << raw_config->waitBeforeFinishDetectionSeconds << std::endl;

    std::cout << "sizeof(SharedConfig): " << sizeof(SharedConfig) << " bytes" << std::endl;

    std::cout << "Offsets in SharedConfig:" << std::endl;
    std::cout << "startRace: " << offsetof(SharedConfig, startRace) << std::endl;
    std::cout << "enableCarEngine: " << offsetof(SharedConfig, enableCarEngine) << std::endl;
    std::cout << "enableCarSteering: " << offsetof(SharedConfig, enableCarSteering) << std::endl;
    std::cout << "enableCameraThresholdCheck: " << offsetof(SharedConfig, enableCameraThresholdCheck) << std::endl;
    std::cout << "enableFinishLineDetection: " << offsetof(SharedConfig, enableFinishLineDetection) << std::endl;
    std::cout << "currentState: " << offsetof(SharedConfig, currentState) << std::endl;
    std::cout << "thresholdValue: " << offsetof(SharedConfig, thresholdValue) << std::endl;
    std::cout << "distanceErrorFromChassis: " << offsetof(SharedConfig, distanceErrorFromChassis) << std::endl;
    std::cout << "lineMinPixelCount: " << offsetof(SharedConfig, lineMinPixelCount) << std::endl;
    std::cout << "distanceSensorError: " << offsetof(SharedConfig, distanceSensorError) << std::endl;
    std::cout << "stoppingDistanceBoxFrontEnd: " << offsetof(SharedConfig, stoppingDistanceBoxFrontEnd) << std::endl;
    std::cout << "interpolatedPointsSetup: " << offsetof(SharedConfig, interpolatedPointsSetup) << std::endl;

    std::cout << "calibrateTopLinePerc: " << offsetof(SharedConfig, calibrateTopLinePerc) << std::endl;
    std::cout << "calibrateBottomLinePerc: " << offsetof(SharedConfig, calibrateBottomLinePerc) << std::endl;
    std::cout << "trackLaneWidthOffset: " << offsetof(SharedConfig, trackLaneWidthOffset) << std::endl;
    std::cout << "topImageCutPercentage: " << offsetof(SharedConfig, topImageCutPercentage) << std::endl;
    std::cout << "topCutOffPercentageCustomConnected: " << offsetof(SharedConfig, topCutOffPercentageCustomConnected) << std::endl;
    std::cout << "lineStartPointY: " << offsetof(SharedConfig, lineStartPointY) << std::endl;
    std::cout << "line90DegreeAngleRange: " << offsetof(SharedConfig, line90DegreeAngleRange) << std::endl;
    std::cout << "finishLineAngleRange: " << offsetof(SharedConfig, finishLineAngleRange) << std::endl;
    std::cout << "servoTurnAdjustmentCoefficient: " << offsetof(SharedConfig, servoTurnAdjustmentCoefficient) << std::endl;
    std::cout << "corneringSpeedCoefficient: " << offsetof(SharedConfig, corneringSpeedCoefficient) << std::endl;
    std::cout << "minSpeed: " << offsetof(SharedConfig, minSpeed) << std::endl;
    std::cout << "maxSpeed: " << offsetof(SharedConfig, maxSpeed) << std::endl;
    std::cout << "currentEdfFanSpeed: " << offsetof(SharedConfig, currentEdfFanSpeed) << std::endl;
    std::cout << "curvatureFactor: " << offsetof(SharedConfig, curvatureFactor) << std::endl;
    std::cout << "rdp_epsilon: " << offsetof(SharedConfig, rdp_epsilon) << std::endl;
    std::cout << "boostSpeedValue: " << offsetof(SharedConfig, boostSpeedValue) << std::endl;
    std::cout << "minAngleLookAheadReference: " << offsetof(SharedConfig, minAngleLookAheadReference) << std::endl;
    std::cout << "maxAngleLookAheadReference: " << offsetof(SharedConfig, maxAngleLookAheadReference) << std::endl;
    std::cout << "minLookAheadInCm: " << offsetof(SharedConfig, minLookAheadInCm) << std::endl;
    std::cout << "maxLookAheadInCm: " << offsetof(SharedConfig, maxLookAheadInCm) << std::endl;
    std::cout << "waitBeforeStartSeconds: " << offsetof(SharedConfig, waitBeforeStartSeconds) << std::endl;
    std::cout << "waitBeforeEdfStartSeconds: " << offsetof(SharedConfig, waitBeforeEdfStartSeconds) << std::endl;
    std::cout << "waitBeforeFinishDetectionSeconds: " << offsetof(SharedConfig, waitBeforeFinishDetectionSeconds) << std::endl;

    std::cout << "sizeof(SharedConfig): " << sizeof(SharedConfig) << " bytes" << std::endl;

    std::thread buttonThread(checkButtonPress);
    
    #if 1 == ENABLE_TCP_SITE_DEBUG 
        std::thread websiteTCPThread(websiteTCPLoop, std::ref(websiteTCP));
    #endif
    try {

        #if 1 == ENABLE_CAMERA_STREAMING
            // Get the camera index from the shell scriptsc
            std::string cameraIndexStr = getCameraIndex();
            int cameraIndex = std::stoi(cameraIndexStr);
            std::cout << "cameraIndex: " << cameraIndex << std::endl;
            // Initialize the global camera instance
            global_camera = std::make_shared<CameraProcessing>(cameraIndex, captureFrameWidth, captureFrameHeight, captureFps, global_config);
        #else
        
            // Initialize the global camera instance
            global_camera = std::make_shared<CameraProcessing>(global_config);
        #endif

        global_camera->startCapture();
        global_camera->startFrameProcessing();

        
        while (global_camera->isRunning()) {
            std::this_thread::sleep_for(std::chrono::milliseconds(100));
        }

        app_running = false;

        if (buttonThread.joinable()) {
            buttonThread.join();
        }

        #if 1 == ENABLE_TCP_SITE_DEBUG 
        
            websiteTCP.close(); 
            if (websiteTCPThread.joinable()) {
                websiteTCPThread.join();
            }
        #endif

    } catch (const std::exception& e) {
        std::cerr << "Exception: " << e.what() << std::endl;
        return -1;
    }

    return 0;
}

// void signalHandler(int signal) {
//     std::cout << "\nReceived signal " << signal << ". Stopping camera..." << std::endl;

//     if (global_camera) {
//         global_camera->stopCapture();
//         global_camera->stopFrameProcessing();
//     }
//     #if 1 == ENABLE_TEENSY_SERIAL
//         int checksum = 0;
//         std::string serialString = "0;0;0;0;0;0;0;0;0;0";
//         for (char c : serialString) {
//             checksum += static_cast<unsigned char>(c);
//         }

//         serialString += ";" + std::to_string(checksum);
//         serial.writeToSerial(serialString);
//         serial.disconnectTeensy();
//     #endif

//     std::exit(signal);
//}

void signalHandler(int signal) {
    const char* crashMsg = "\n[FATAL] Signal received. Sending hard hardware kill...\n";
    write(STDOUT_FILENO, crashMsg, strlen(crashMsg));

    if (global_camera) {
        global_camera->stopCapture();
        global_camera->stopFrameProcessing();
    }

    #if 1 == ENABLE_TEENSY_SERIAL
        // Grab the singleton instance
        debix::SerialPort& serial = debix::SerialPort::getInstance();
        int fd = serial.getFileDescriptor(); 
        
        if (fd >= 0) {
            // Hardcoded string: "0;0;0;0;0;0;0;0;0;0;1011\n"
            // (1011 is the pre-calculated ASCII checksum of the ten zeros and nine semicolons)
            const char* emergencyCmd = "0;0;0;0;0;0;0;0;0;0;1011\n";
            
            write(fd, emergencyCmd, strlen(emergencyCmd));
        }
    #endif
    _exit(signal); 
}

void stopChildProcess() {
    if (child_pid > 0) {
        std::cout << "Stopping Python process (PID: " << child_pid.load() << ")" << std::endl;
        kill(child_pid, SIGTERM);  // Graceful stop
        waitpid(child_pid, NULL, 0);  // Cleanup zombie process
        child_pid = -1;  // Reset PID to allow restarting
    }
}

void checkButtonPress() {
    gpiod_chip *chip = nullptr;
    gpiod_line *line = nullptr;

    // Open GPIO only once at the start
    chip = gpiod_chip_open("/dev/gpiochip0");
    if (!chip) {
        std::cerr << "Failed to open GPIO chip!" << std::endl;
        return;
    }

    line = gpiod_chip_get_line(chip, SW_LINE);
    if (!line) {
        std::cerr << "Failed to get GPIO line!" << std::endl;
        gpiod_chip_close(chip);
        return;
    }

    if (gpiod_line_request_input(line, "button_reader") < 0) {
        std::cerr << "Failed to set GPIO as input!" << std::endl;
        gpiod_chip_close(chip);
        return;
    }

    while (true) {
        if(line != nullptr){
            int button_state = gpiod_line_get_value(line);
        
            if (button_state == 0 && child_pid.load() == -1) { 
                std::cout << "Button pressed! Starting menu_rotary.py..." << std::endl;

                // Releasing GPIO before starting Python
                gpiod_line_release(line);
                gpiod_chip_close(chip);
                chip = nullptr;
                line = nullptr;

                pid_t pid = fork();

                if (pid == 0) {  // Child process
                    execlp("python3", "python3", "menu_rotary.py", NULL);
                    std::cerr << "Failed to execute menu_rotary.py" << std::endl;
                    exit(1);
                } else if (pid > 0) {
                    child_pid = pid;  // Store new child PID
                }
            }
        }

        // Check if Python exited and reinitialize GPIO
        if (child_pid.load() > 0) {
            int status;
            pid_t result = waitpid(child_pid.load(), &status, WNOHANG);
            if (result > 0) {
                std::cout << "Python process (PID: " << child_pid.load() << ") has exited. Cleaning up." << std::endl;
                child_pid = -1;  // Reset child process ID

                // Reinitializing GPIO after Python exits
                chip = gpiod_chip_open("/dev/gpiochip0");
                if (!chip) {
                    std::cerr << "Failed to open GPIO chip!" << std::endl;
                    return;
                }

                line = gpiod_chip_get_line(chip, SW_LINE);
                if (!line) {
                    std::cerr << "Failed to get GPIO line!" << std::endl;
                    gpiod_chip_close(chip);
                    return;
                }

                if (gpiod_line_request_input(line, "button_reader") < 0) {
                    std::cerr << "Failed to set GPIO as input!" << std::endl;
                    gpiod_chip_close(chip);
                    return;
                }
            }
        }

        std::this_thread::sleep_for(std::chrono::milliseconds(200));  // Check button every 200ms
    }

    gpiod_line_release(line);
    gpiod_chip_close(chip);
}

// void websiteTCPLoop(TcpConnection& connection)
// {
//     while (app_running) {
//         std::string command = connection.receiveStringData();

//         if (command.empty() || !app_running) {
//             std::cout << "[Website] TCP connection closed or shutting down.\n";
//             break; 
//         }

//         if (command == "STOP") 
//         {
//             global_config->enableCarEngine = 0;
//             global_config->currentEdfFanSpeed = 0;
//             global_config->enableFinishLineDetection = 0;
//             global_config->startRace = 0;
//         }
//         else if(command == "READ") 
//         {
//             SharedConfig* raw_config = global_config.get();
//             std::string jsonStr = json(*raw_config).dump();
//             connection.sendStringData(jsonStr + "\n");  // Ensure newline if you're using read_until
//             std::cout << "[Website] Sent config JSON.\n";
//         }
//         else if (command.rfind("WRITE:", 0) == 0) {
//             std::string jsonStr = command.substr(6);  // Remove "WRITE:"
//             try {
//                 SharedConfig newConfig = json::parse(jsonStr);
//                 *global_config = newConfig;
//                 std::cout << "[Website] Updated config from web.\n";
//             } catch (const std::exception& e) {
//                 std::cerr << "[Website] Failed to parse config: " << e.what() << std::endl;
//             }
//         } 
//         else 
//         {
//             std::cerr << "[Website] Unknown command: " << command << std::endl;
//         }
//     }
// }


void websiteTCPLoop(TcpConnection& connection)
{
    try {
        while (app_running) {
            std::string command = connection.receiveStringData();

            if (command.empty() || !app_running) {
                std::cout << "[Website] TCP connection closed or shutting down.\n";
                break; 
            }

            if (command == "STOP") 
            {
                global_config->enableCarEngine = 0;
                global_config->currentEdfFanSpeed = 0;
                global_config->enableFinishLineDetection = 0;
                global_config->startRace = 0;
            }
            else if(command == "READ") 
            {
                SharedConfig* raw_config = global_config.get();
                std::string jsonStr = json(*raw_config).dump();
                connection.sendStringData(jsonStr + "\n");  
                std::cout << "[Website] Sent config JSON.\n";
            }
            else if (command.rfind("WRITE:", 0) == 0) {
                std::string jsonStr = command.substr(6);  // Remove "WRITE:"
                try {
                    SharedConfig newConfig = json::parse(jsonStr);
                    
                    // 2. ADDED MUTEX LOCK: This prevents your camera thread from 
                    // reading half-written data while you overwrite the struct!
                    {
                        std::lock_guard<std::mutex> lock(configMutex);
                        *global_config = newConfig;
                    }
                    
                    std::cout << "[Website] Updated config from web.\n";
                } catch (const std::exception& e) {
                    std::cerr << "[Website] Failed to parse config: " << e.what() << std::endl;
                }
            } 
            else 
            {
                std::cerr << "[Website] Unknown command: " << command << std::endl;
            }
        }
    } 
    // Catches the boost::system::system_error (and others) triggered by socket.close()
    catch (const std::exception& e) {
        std::cout << "[Website] TCP loop interrupted and closed cleanly (" << e.what() << ").\n";
    }
}

bool isValidConfig(const SharedConfig& config) {
    std::cout << "config.line90DegreeAngleRange:" << config.line90DegreeAngleRange << "\n";
    return (
        config.startRace >= 0 && config.startRace <= 1 &&
        config.enableCarEngine >= 0 && config.enableCarEngine <= 1 &&
        config.enableCarSteering >= 0 && config.enableCarSteering <= 1 &&
        config.thresholdValue >= 0 && config.thresholdValue <= 255 &&
        config.distanceErrorFromChassis >= -240 && config.distanceErrorFromChassis <= 240 &&
        config.lineMinPixelCount >= 0 && config.lineMinPixelCount <= 255 &&
        config.distanceSensorError >= 0 && config.distanceSensorError <= 30 &&
        config.stoppingDistanceBoxFrontEnd >= 1 && config.stoppingDistanceBoxFrontEnd <= 30 &&
        config.interpolatedPointsSetup >= 0 && config.interpolatedPointsSetup <= 1 &&
        config.calibrateTopLinePerc >= 0.0 && config.calibrateTopLinePerc <= 100.0 &&
        config.calibrateBottomLinePerc >= 0.0 && config.calibrateBottomLinePerc <= 100.0 &&
        config.trackLaneWidthOffset >= -100.0 && config.trackLaneWidthOffset <= 200.0 &&
        config.topImageCutPercentage >= 0.0 && config.topImageCutPercentage <= 1.0 &&
        config.topCutOffPercentageCustomConnected >= 0.0 && config.topCutOffPercentageCustomConnected <= 1.0 &&
        config.lineStartPointY >= 0.0 && config.lineStartPointY <= 1.0 &&
        config.line90DegreeAngleRange >= 0.0 && config.line90DegreeAngleRange <= 90.0 &&
        config.finishLineAngleRange >= 90.0 && config.finishLineAngleRange <= 180.0 &&
        config.servoTurnAdjustmentCoefficient >= 0.0 && config.servoTurnAdjustmentCoefficient <= 5.0 &&
        config.corneringSpeedCoefficient >= 0.0 && config.corneringSpeedCoefficient <= 2.0 &&
        config.minSpeed >= 0.0 && config.minSpeed <= 500.0 &&
        config.maxSpeed >= 0.0 && config.maxSpeed <= 500.0 &&
        config.minSpeedAfterFinish >= 0.0 && config.minSpeedAfterFinish <= 350.0 &&
        config.maxSpeedAfterFinish >= 0.0 && config.maxSpeedAfterFinish <= 350.0 &&
        config.currentEdfFanSpeed >= 0.0 && config.currentEdfFanSpeed <= 500.0 &&
        config.curvatureFactor >= 0.0 && config.curvatureFactor <= 200.0 &&
        config.rdp_epsilon >= 0.0 && config.rdp_epsilon <= 25.0 &&
        config.boostSpeedValue >= 0.0 && config.boostSpeedValue <= 500.0 &&
        config.minAngleLookAheadReference >= 0.0 && config.minAngleLookAheadReference <= 4000.0 &&
        config.maxAngleLookAheadReference >= 0.0 && config.maxAngleLookAheadReference <= 4000.0 &&
        config.minLookAheadInCm >= 0.0 && config.minLookAheadInCm <= 100.0 &&
        config.maxLookAheadInCm >= 0.0 && config.maxLookAheadInCm <= 100.0 &&
        config.waitBeforeStartSeconds >= 0.0 && config.waitBeforeStartSeconds <= 10.0 &&
        config.waitBeforeEdfStartSeconds >= 0.0 && config.waitBeforeEdfStartSeconds <= 5.0 &&
        config.waitBeforeFinishDetectionSeconds >= 0.0 && config.waitBeforeFinishDetectionSeconds <= 20.0
    );
}
