gulyasyalex/Proiect-NXP-CUP-2025-/include/mathFunctions.h

#ifndef MATH_FUNCTIONS_H
#define MATH_FUNCTIONS_H

#include <opencv2/opencv.hpp>
#include <cmath>
#include "config.h"

#include <sstream>
#include <iomanip>
#include <string>

double lineLength(const cv::Vec4i& line);
double euclideanDistance(cv::Point2f p1, cv::Point2f p2);
double euclideanDistanceCoord(int x1, int y1, int x2, int y2);
double calculateSignedAngle(cv::Point2f p1, cv::Point2f p2, cv::Point2f p3);
double mapAngleToServo(double angle);
cv::Point2f calculateMidpoint(const cv::Point2f& p1, const cv::Point2f& p2);
cv::Point2f calculateCentroid(const std::vector<cv::Point2f>& line);
std::vector<cv::Point2f> generateNeighborhood(int radius);
std::vector<cv::Point2f> closestSegmentOnCurve(const std::vector<cv::Point2f>& curve, const cv::Point2f& point);
double angleBetweenVectors(const cv::Point2f& v1, const cv::Point2f& v2);
double roundToTwoDecimals(double value);
std::string to_string_with_precision(double value, int precision);

// Function to calculate the length of a line
double lineLength(const cv::Vec4i& line) {
    int x1 = line[0], y1 = line[1], x2 = line[2], y2 = line[3];
    return sqrt((x2 - x1) * (x2 - x1) + (y2 - y1) * (y2 - y1));
}
// Function to calculate the Euclidean distance between two OpenCv points
double euclideanDistance(cv::Point2f p1, cv::Point2f p2) {
   return std::hypot(p1.x - p2.x, p1.y - p2.y);
}
// Function to calculate the Euclidean distance between two points in coordinate values
double euclideanDistanceCoord(int x1, int y1, int x2, int y2) {
    return std::hypot(x1 - x2, y1 - y2);
}

// Function to calculate the signed angle between three points 
double calculateSignedAngle(cv::Point2f p1, cv::Point2f p2, cv::Point2f p3)
{
    cv::Point2f vec1 = p1 - p2; // Vector de la p2 la p1
    cv::Point2f vec2 = p3 - p2; // Vector de la p2 la p3
    double dotProduct = vec1.x * vec2.x + vec1.y * vec2.y;
    double crossProduct = vec1.x * vec2.y - vec1.y * vec2.x;
    //double angle = std::atan2(crossProduct, dotProduct) * 180.0 / CV_PI;
    double angle = std::atan2(crossProduct, dotProduct);
    return angle;
}

// Function to calculate the midpoint between two points
cv::Point2f calculateMidpoint(const cv::Point2f& p1, const cv::Point2f& p2) 
{
    return cv::Point2f((p1.x + p2.x) / 2, (p1.y + p2.y) / 2);
}
// Function to calculate the centroid of a line (average of the points)
cv::Point2f calculateCentroid(const std::vector<cv::Point2f>& line) 
{
    cv::Point2f centroid(0, 0);
    for (const auto& point : line) {
        centroid.x += point.x;
        centroid.y += point.y;
    }
    centroid.x /= line.size();
    centroid.y /= line.size();
    return centroid;
}
// Function that generates a radius of values for customConnectedComponentsWithThreshold
std::vector<cv::Point2f> generateNeighborhood(int radius) 
{
    std::vector<cv::Point2f> neighbors;
    for (int dy = -radius; dy <= radius; ++dy) {
        for (int dx = -radius; dx <= radius; ++dx) {
            if (std::sqrt(dx * dx + dy * dy) <= radius) { // Ensure point lies within the circle
                neighbors.emplace_back(dx, dy);
            }
        }
    }
    return neighbors;
}

// Function to find the closest segment as a vector of two points
std::vector<cv::Point2f> closestSegmentOnCurve(const std::vector<cv::Point2f>& curve, const cv::Point2f& point) 
{
    double minDistance = std::numeric_limits<double>::max();
    std::vector<cv::Point2f> bestSegment(2); // Stores the closest segment

    for (size_t i = 0; i < curve.size() - 1; ++i) {
        cv::Point2f p1 = curve[i];
        cv::Point2f p2 = curve[i + 1];

        // Compute the projection of the point onto the segment
        cv::Point2f lineVec = p2 - p1;
        cv::Point2f pointVec = point - p1;
        float t = lineVec.dot(pointVec) / lineVec.dot(lineVec);

        cv::Point2f closestPoint;
        if (t < 0.0f) {
            closestPoint = p1;
        } else if (t > 1.0f) {
            closestPoint = p2;
        } else {
            closestPoint = p1 + t * lineVec;
        }

        double dist = euclideanDistance(point, closestPoint);
        if (dist < minDistance) {
            minDistance = dist;
            bestSegment[0] = p1;
            bestSegment[1] = p2;
        }
    }
    return bestSegment;
}


// Function to compute the angle between two vectors
double angleBetweenVectors(const cv::Point2f& v1, const cv::Point2f& v2) 
{
    double dot = v1.x * v2.x + v1.y * v2.y;
    double mag1 = std::sqrt(v1.x * v1.x + v1.y * v1.y);
    double mag2 = std::sqrt(v2.x * v2.x + v2.y * v2.y);
    
    return std::acos(dot / (mag1 * mag2)) * 180.0 / CV_PI;
}

double roundToTwoDecimals(double value) {
    return std::round(value * 100.0) / 100.0;
}

std::string to_string_with_precision(double value, int precision = 2) {
    std::ostringstream stream;
    stream << std::fixed << std::setprecision(precision) << value;
    return stream.str();
}


#endif
