gulyasyalex/Proiect-NXP-CUP-2025-/Teensy-Code/include/rgb2hsv.h

/*
* Copyright 2023 Constantin Dumitru Petre RĂDULICEA
* 
* Licensed under the Apache License, Version 2.0 (the "License");
* you may not use this file except in compliance with the License.
* You may obtain a copy of the License at
* 
*   http://www.apache.org/licenses/LICENSE-2.0
* 
* Unless required by applicable law or agreed to in writing, software
* distributed under the License is distributed on an "AS IS" BASIS,
* WITHOUT WARRANTIES OR CONDITIONS OF ANY KIND, either express or implied.
* See the License for the specific language governing permissions and
* limitations under the License.
*/

#ifndef __RGB2HSV_H__
#define __RGB2HSV_H__

//#include <stdint>

#define MIN(a,b) (((a)<(b))?(a):(b))
#define MAX(a,b) (((a)>(b))?(a):(b))

typedef struct RGBcolor {
	uint8_t R;
	uint8_t G;
	uint8_t B;
}RGBcolor;

typedef struct HSVcolor {
	float H;
	float S;
	float V;
}HSVcolor;

    static HSVcolor rgb2hsv(RGBcolor rgbColor) {
	//R, G and B input range = 0 � 255
	//H, S and V output range = 0 � 1.0
	HSVcolor hsvColor;
	float del_R, del_G, del_B;

	float var_R = ((float)rgbColor.R / 255.0f);
	float var_G = ((float)rgbColor.G / 255.0f);
	float var_B = ((float)rgbColor.B / 255.0f);

	float var_Min = MIN(MIN(var_R, var_G), var_B);    //Min. value of RGB
	float var_Max = MAX(MAX(var_R, var_G), var_B);    //Max. value of RGB
	float del_Max = var_Max - var_Min;             //Delta RGB value

/*
    Serial.println(rgbColor.R);
    Serial.println(rgbColor.G);
    Serial.println(rgbColor.B);
    Serial.println(var_R);
    Serial.println(var_G);
    Serial.println(var_B);
    Serial.println();
    */

	hsvColor.V = var_Max;
    //Serial.println(hsvColor.V);

		if (del_Max == 0.0f)                     //This is a gray, no chroma...
		{
			hsvColor.H = 0.0f;
			hsvColor.S = 0.0f;
		}
		else                                    //Chromatic data...
		{
			hsvColor.S = del_Max / var_Max;

			del_R = (((var_Max - var_R) / 6.0f) + (del_Max / 2.0f)) / del_Max;
			del_G = (((var_Max - var_G) / 6.0f) + (del_Max / 2.0f)) / del_Max;
			del_B = (((var_Max - var_B) / 6.0f) + (del_Max / 2.0f)) / del_Max;

			if (var_R == var_Max) hsvColor.H = del_B - del_G;
			else if (var_G == var_Max) hsvColor.H = (1.0f / 3.0f) + del_R - del_B;
			else if (var_B == var_Max) hsvColor.H = (2.0f / 3.0f) + del_G - del_R;

			if (hsvColor.H < 0.0f) hsvColor.H += 1.0f;
			if (hsvColor.H > 1.0f) hsvColor.H -= 1.0f;
		}
        
		return hsvColor;
}


#endif
